patrickleboutillier/jcscpu-hmc/Videos/1- Introduction/20201125_134616.jpg

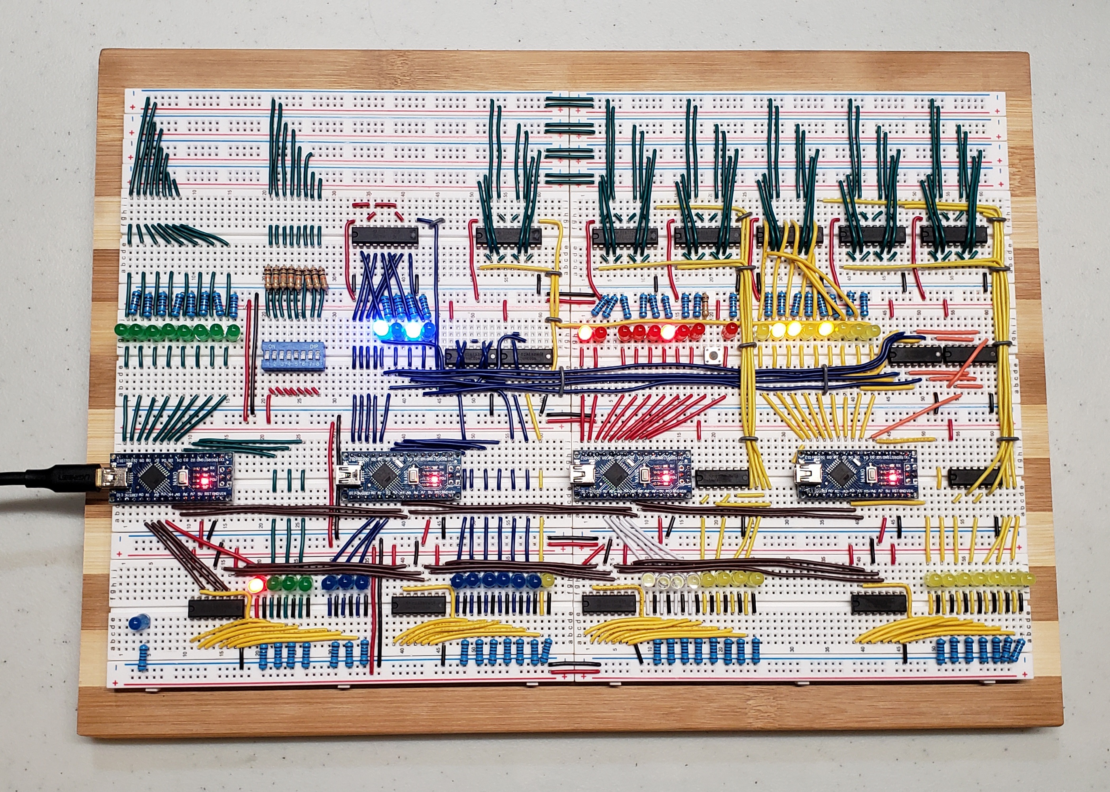
Videos/1- Introduction/20201125_134616.jpg
