patrickleboutillier/jcscpu-hmc/Videos/4- 1-bit Memory/1-bit Memory.png

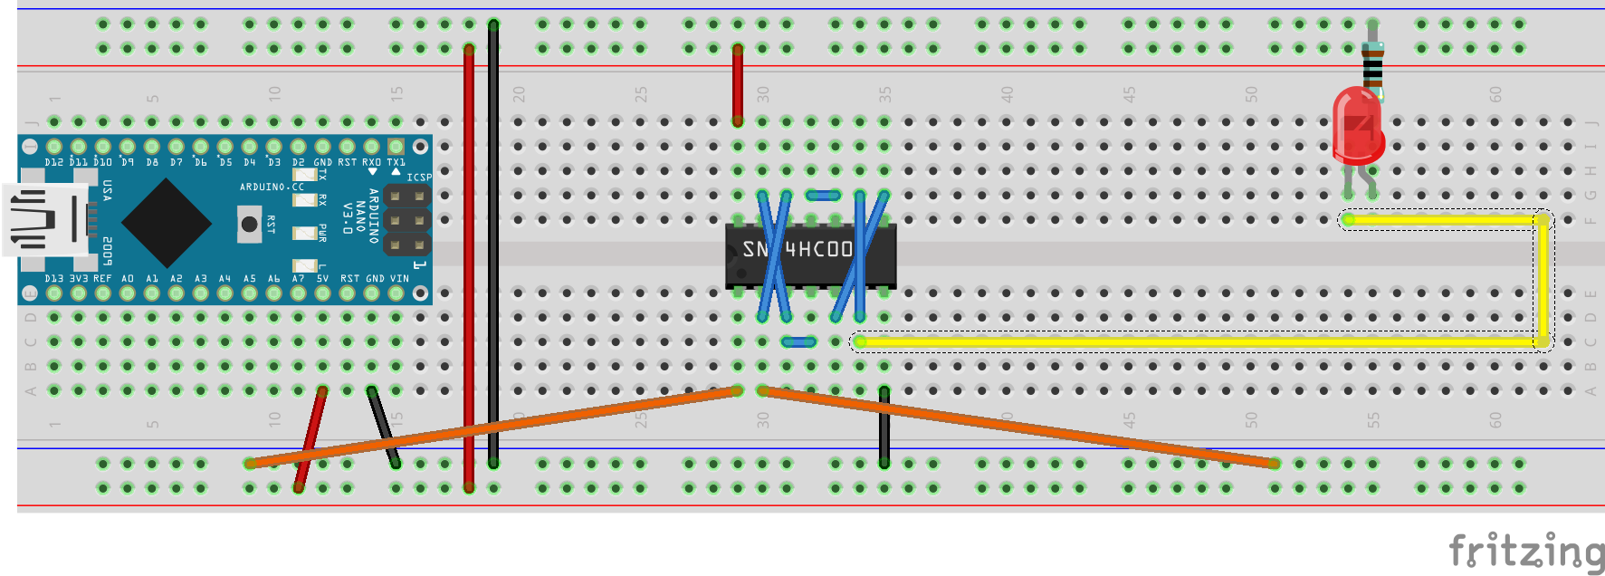
Videos/4- 1-bit Memory/1-bit Memory.png
