patrickleboutillier/jcscpu-hmc/Videos/6- The Register/Register_bb.png

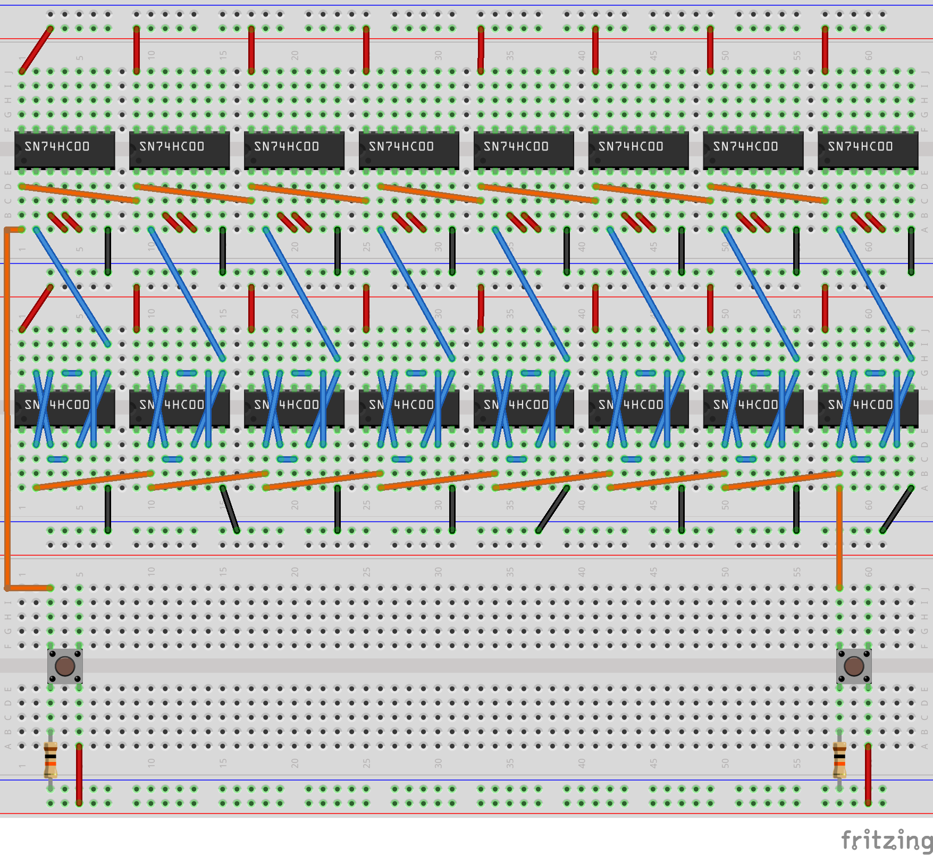
Videos/6- The Register/Register_bb.png
