patrickleboutillier/jcscpu-hmc/Videos/9- The Bus (part 2)/jcscpu-hmc_bb_bus.png

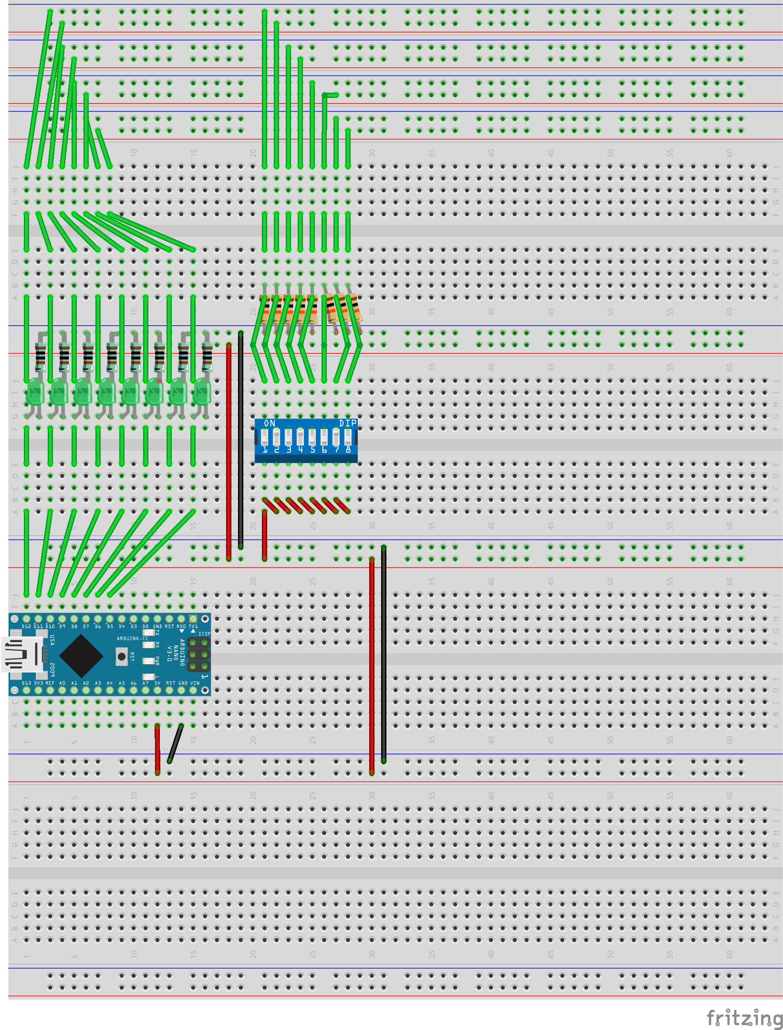
Videos/9- The Bus (part 2)/jcscpu-hmc_bb_bus.png
