patrickleboutillier/jcscpu-hmc/Videos/11- The RAM/jcscpu-hmc_bb_ram.png

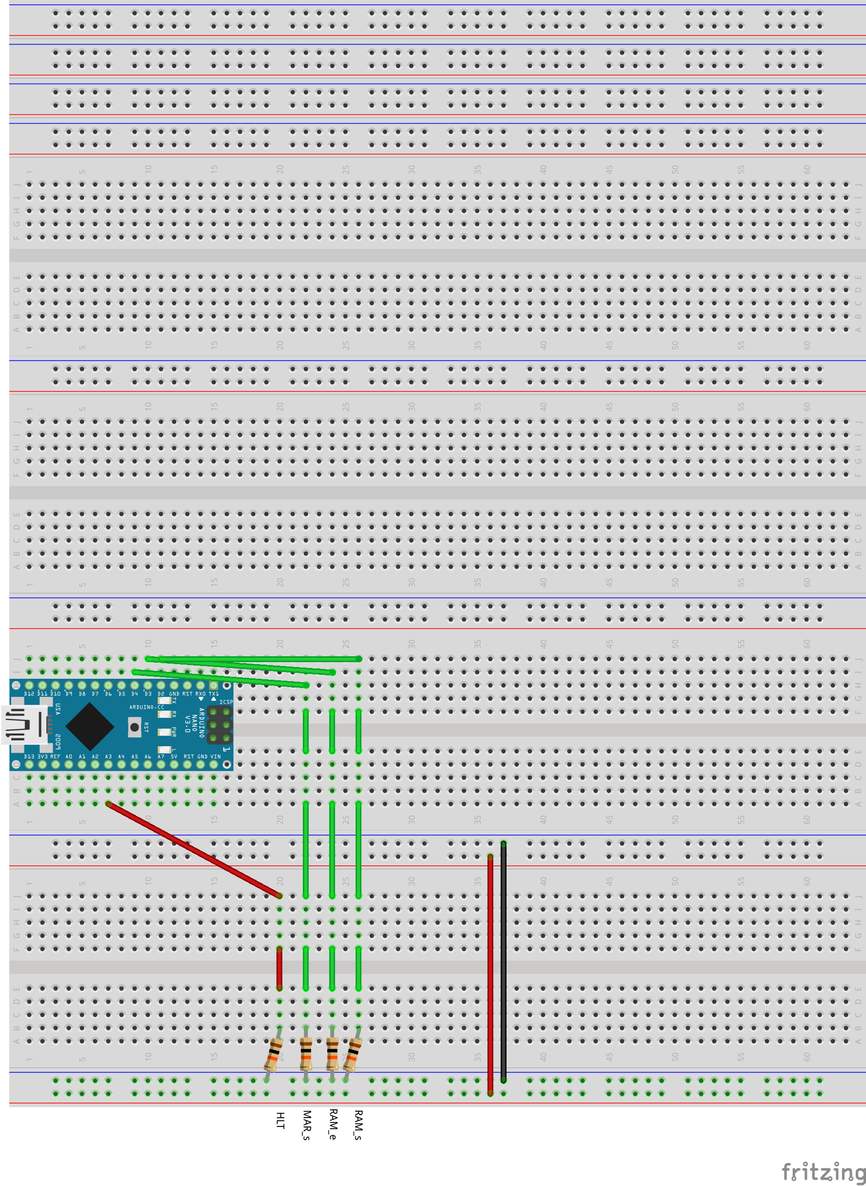
Videos/11- The RAM/jcscpu-hmc_bb_ram.png
