patrickleboutillier/jcscpu-hmc/Videos/11- The RAM/RAM.png

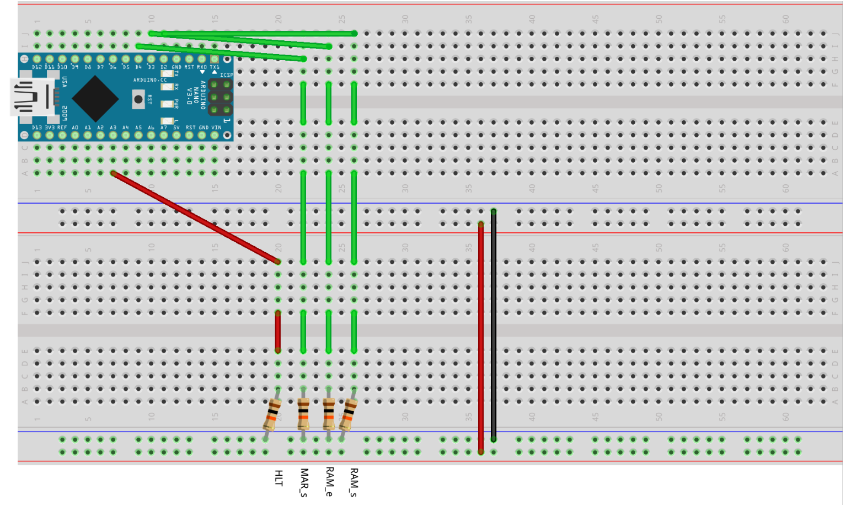
Videos/11- The RAM/RAM.png
