patrickleboutillier/jcscpu-hmc/Videos/11- The RAM/RAM_code.png

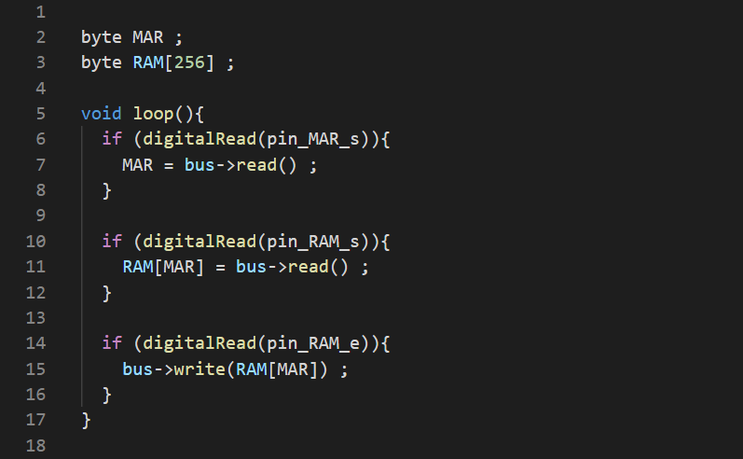
Videos/11- The RAM/RAM_code.png
