patrickleboutillier/jcscpu-hmc/Videos/13- The ALU (part1)/BOT.png

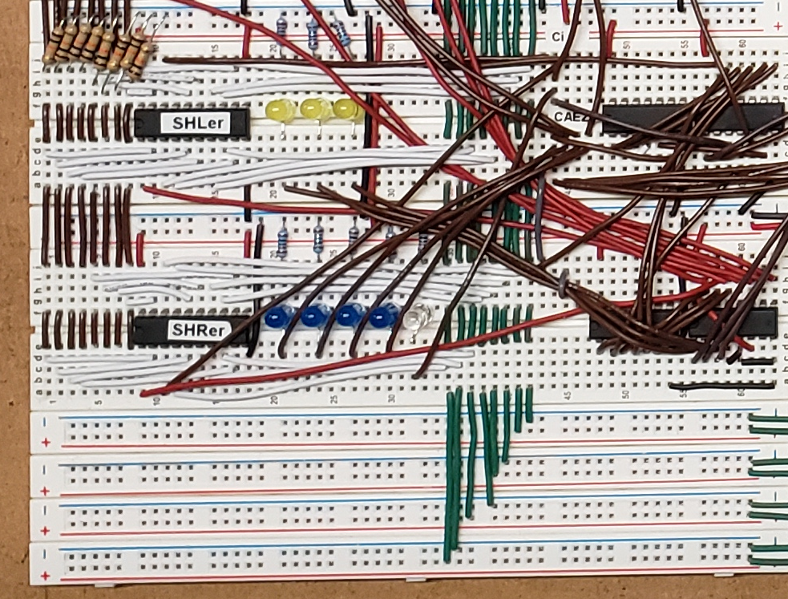
Videos/13- The ALU (part1)/BOT.png
