patrickleboutillier/jcscpu-hmc/Videos/13- The ALU (part1)/MID1.png

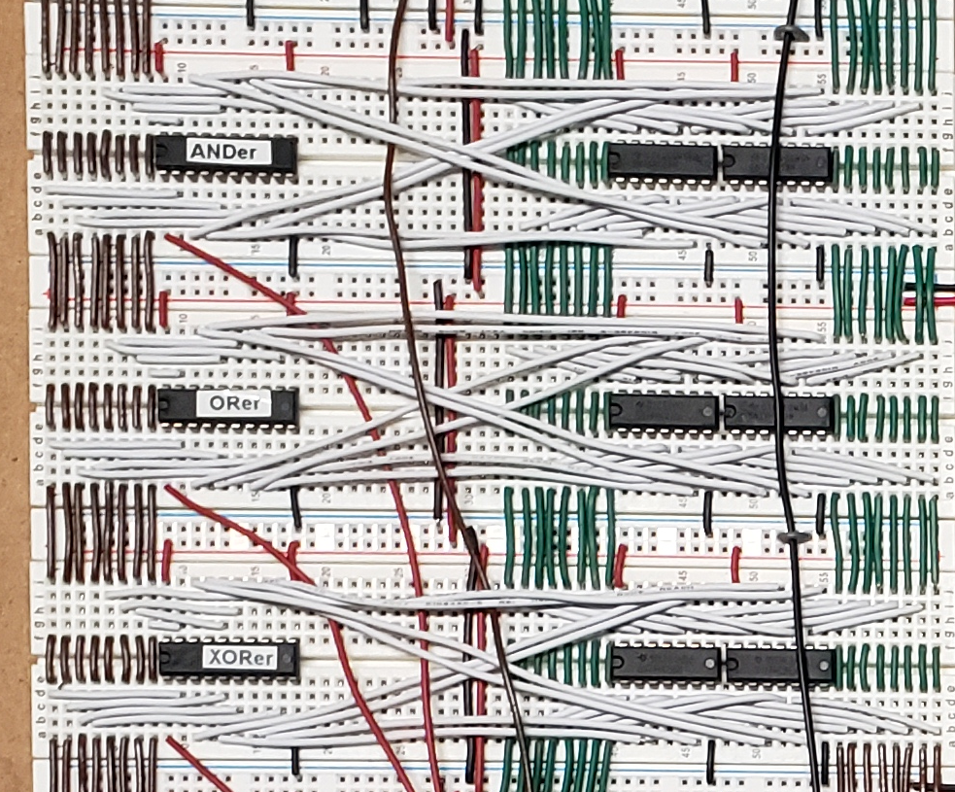
Videos/13- The ALU (part1)/MID1.png
