patrickleboutillier/jcscpu-hmc/Videos/13- The ALU (part1)/MID2.png

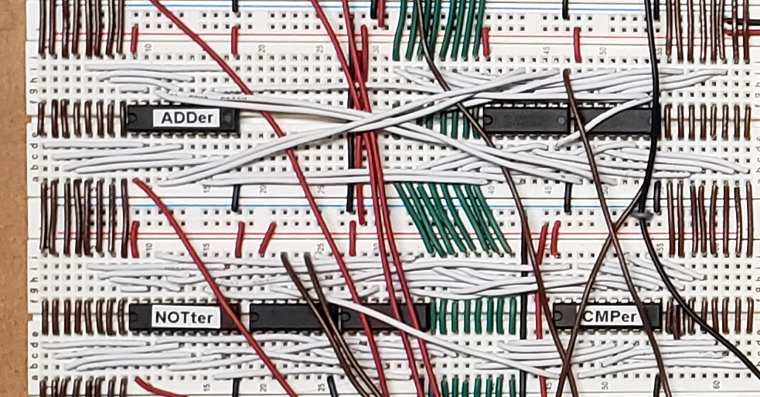
Videos/13- The ALU (part1)/MID2.png
