patrickleboutillier/jcscpu-hmc/Videos/13- The ALU (part1)/TOP.png

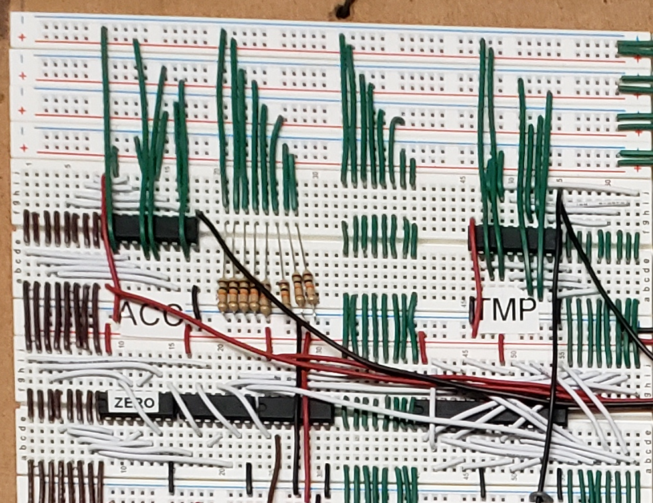
Videos/13- The ALU (part1)/TOP.png
