patrickleboutillier/jcscpu-hmc/Videos/14- The ALU (part 2)/ALU_code_1.png

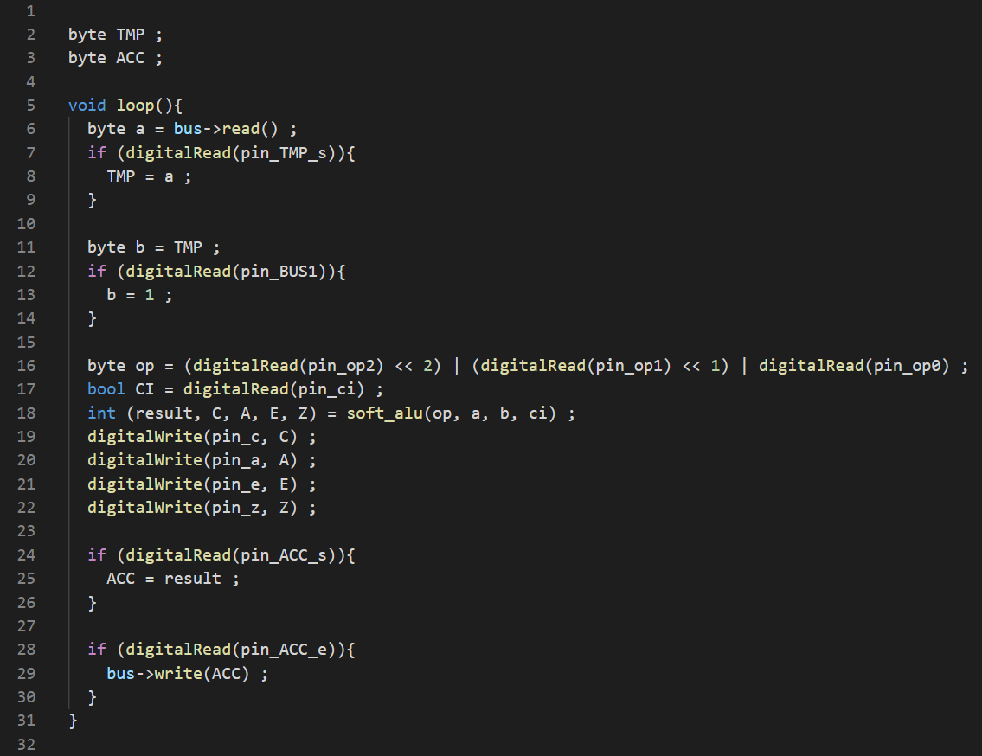
Videos/14- The ALU (part 2)/ALU_code_1.png
