patrickleboutillier/jcscpu-hmc/Videos/14- The ALU (part 2)/jcscpu-hmc_alu_bb.png

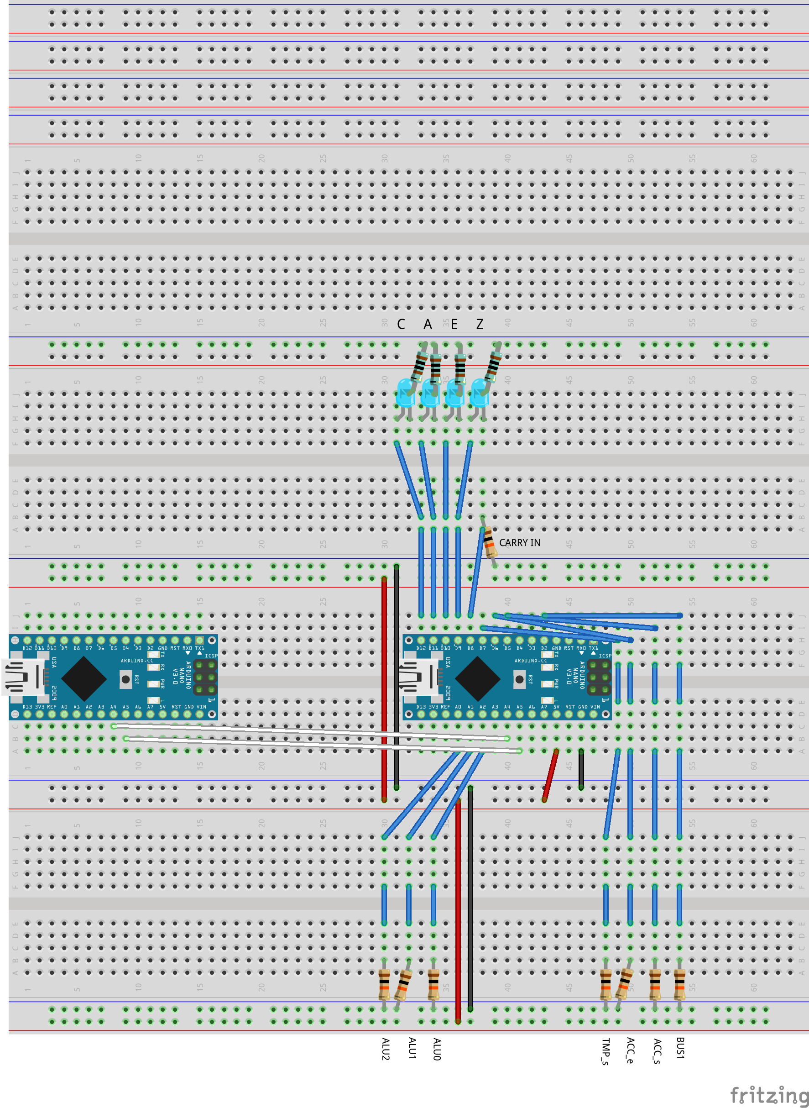
Videos/14- The ALU (part 2)/jcscpu-hmc_alu_bb.png
