patrickleboutillier/jcscpu-hmc/Videos/14- The ALU (part 2)/jcscpu-hmc_alu_bb_crop.png

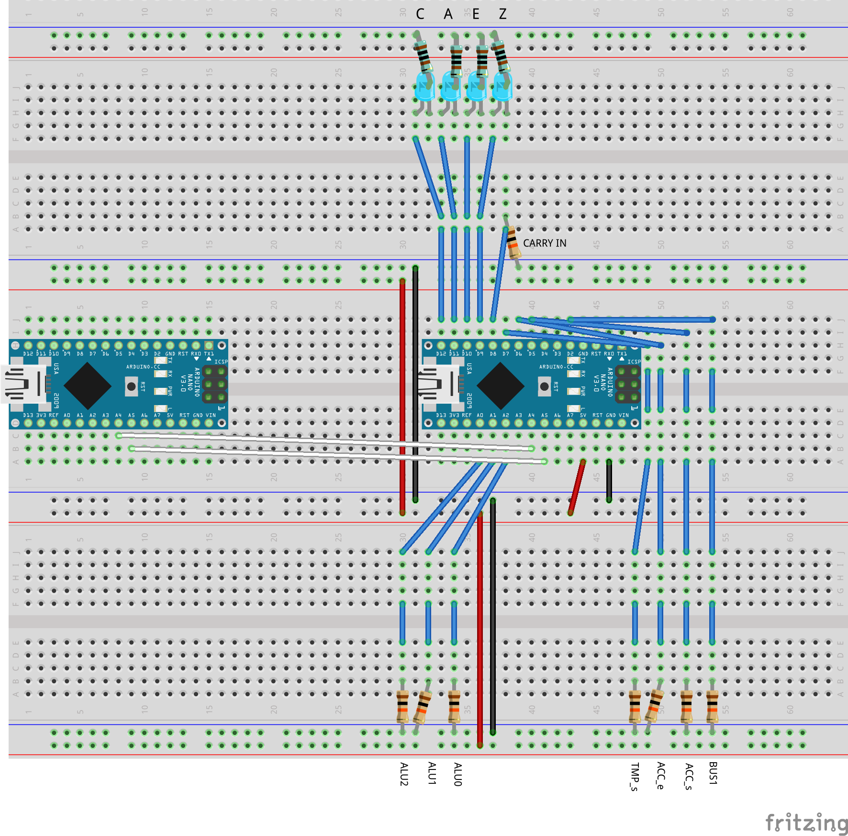
Videos/14- The ALU (part 2)/jcscpu-hmc_alu_bb_crop.png
