patrickleboutillier/jcscpu-hmc/Videos/14- The ALU (part 2)/Table.png

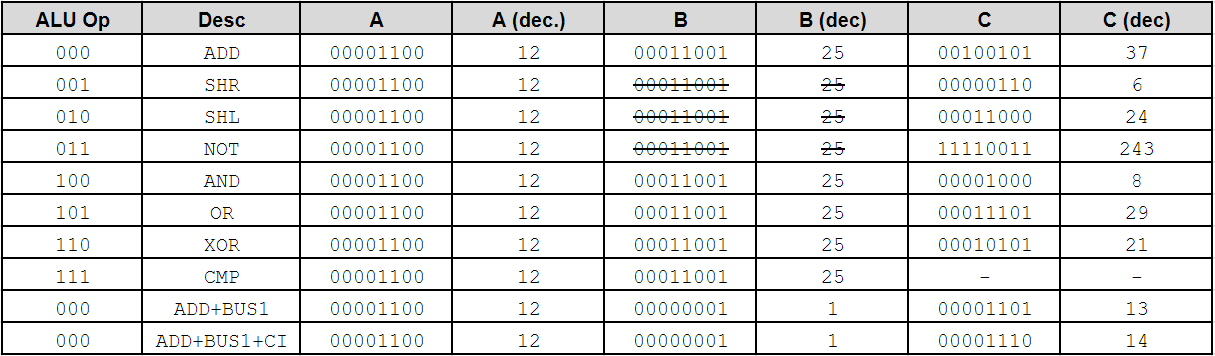
Videos/14- The ALU (part 2)/Table.png
