patrickleboutillier/jcscpu-hmc/Videos/15- The R0 and R1 Registers/jcscpu-hmc_r0r1_bb.png

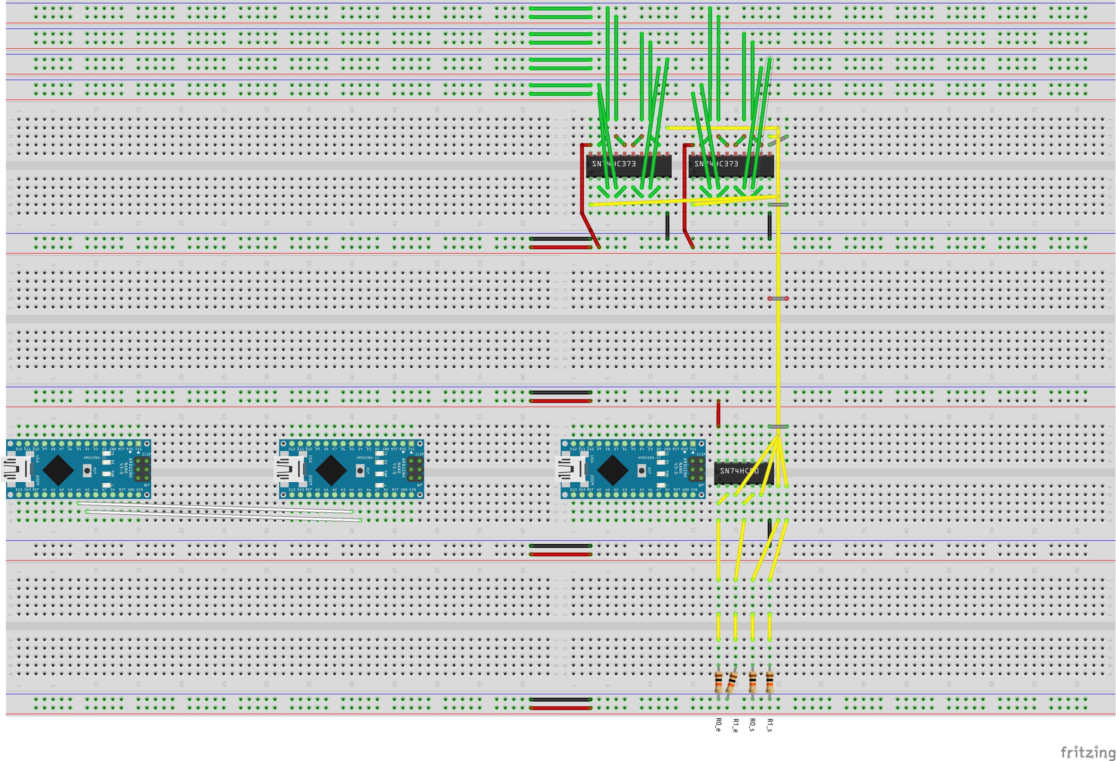
Videos/15- The R0 and R1 Registers/jcscpu-hmc_r0r1_bb.png
