patrickleboutillier/jcscpu-hmc/Videos/16- The Clock and Stepper (part 1)/Clock pulse Generator with CD4049.png

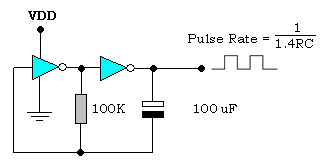
Videos/16- The Clock and Stepper (part 1)/Clock pulse Generator with CD4049.png
