patrickleboutillier/jcscpu-hmc/Videos/16- The Clock and Stepper (part 1)/Digital-Quadrature-Phase-300x210.png

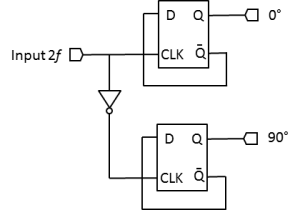
Videos/16- The Clock and Stepper (part 1)/Digital-Quadrature-Phase-300x210.png
