patrickleboutillier/jcscpu-hmc/Videos/16- The Clock and Stepper (part 1)/Flip-Flop-Outputs.png

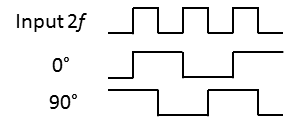
Videos/16- The Clock and Stepper (part 1)/Flip-Flop-Outputs.png
