patrickleboutillier/jcscpu-hmc/Videos/18- The Clock and Stepper (part 3)/jcscpu-hmc_clock_bb_crop.png

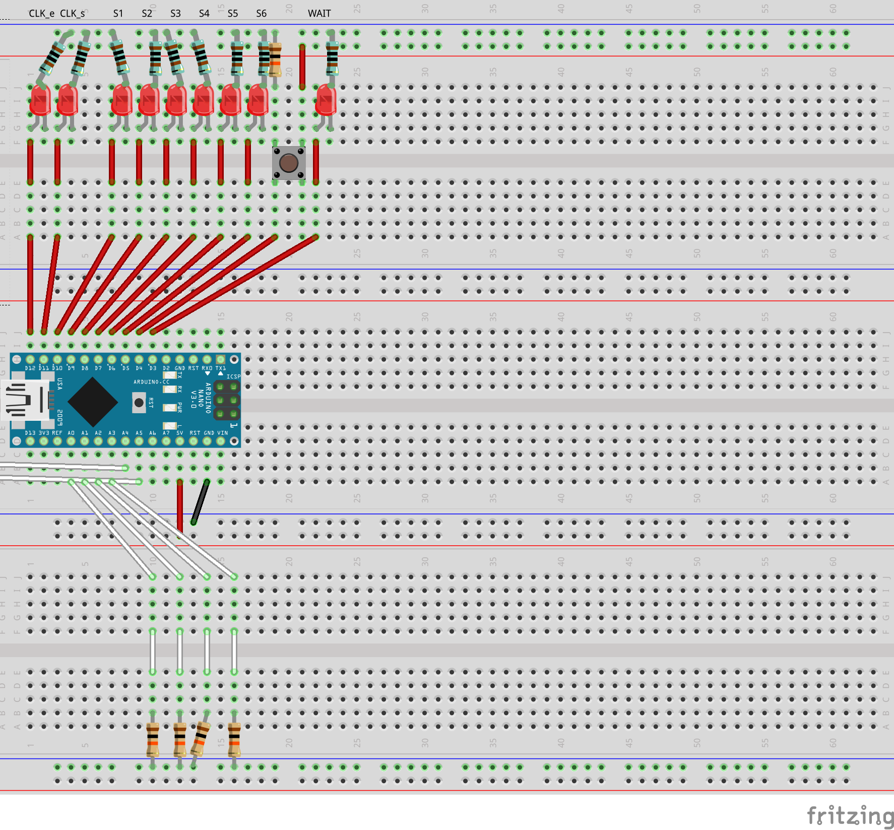
Videos/18- The Clock and Stepper (part 3)/jcscpu-hmc_clock_bb_crop.png
