patrickleboutillier/jcscpu-hmc/Videos/20- The R2 and R3 Registers/jcscpu-hmc_r2r3_bb.png

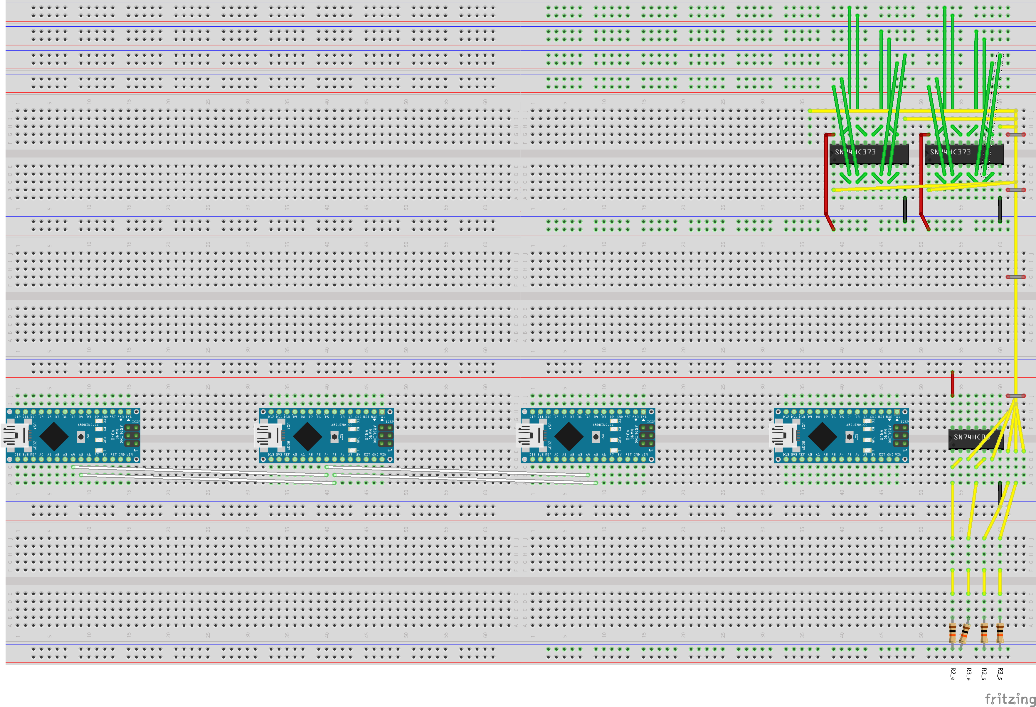
Videos/20- The R2 and R3 Registers/jcscpu-hmc_r2r3_bb.png
