patrickleboutillier/jcscpu-hmc/Videos/23- Microcode/addr0r1.png

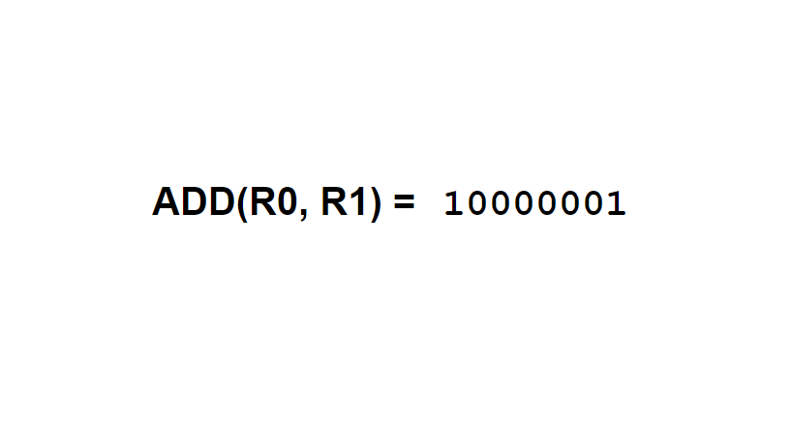
Videos/23- Microcode/addr0r1.png
