patrickleboutillier/jcscpu-hmc/Videos/23- Microcode/Arduino Nano V3.0 Twins Chip 1-550x550.jpg

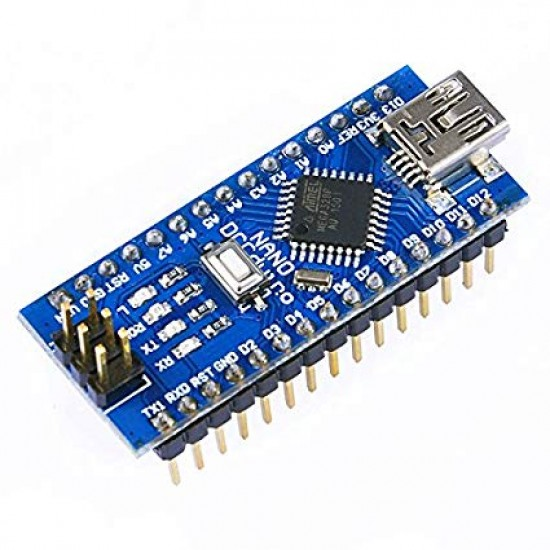
Videos/23- Microcode/Arduino Nano V3.0 Twins Chip 1-550x550.jpg
