patrickleboutillier/jcscpu-hmc/Videos/23- Microcode/CUfunc.png

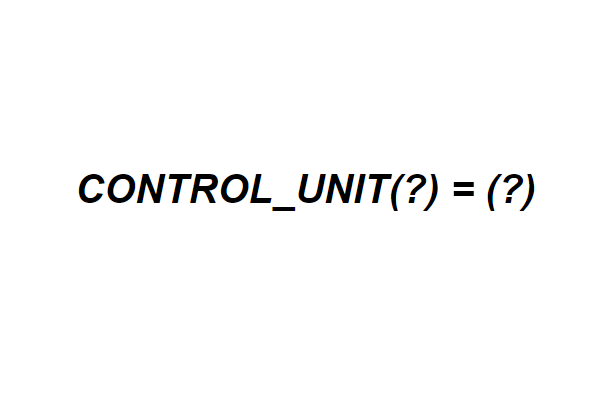
Videos/23- Microcode/CUfunc.png
