patrickleboutillier/jcscpu-hmc/Videos/23- Microcode/CUinput.png

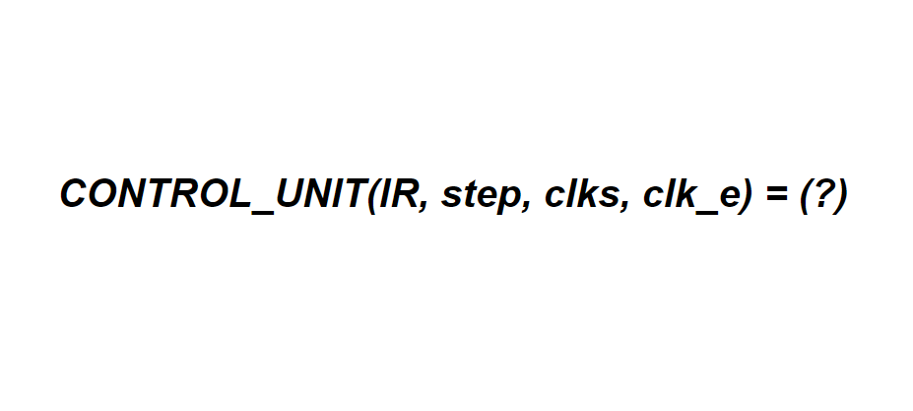
Videos/23- Microcode/CUinput.png
