patrickleboutillier/jcscpu-hmc/Videos/23- Microcode/CUinputoutput.png

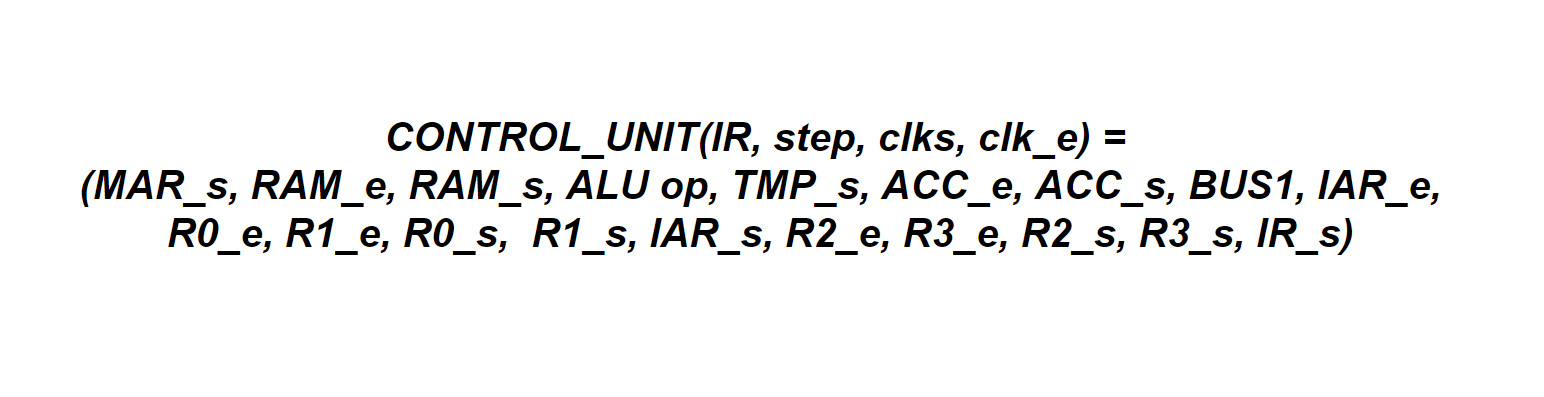
Videos/23- Microcode/CUinputoutput.png
