patrickleboutillier/jcscpu-hmc/Videos/23- Microcode/CUtable1.png

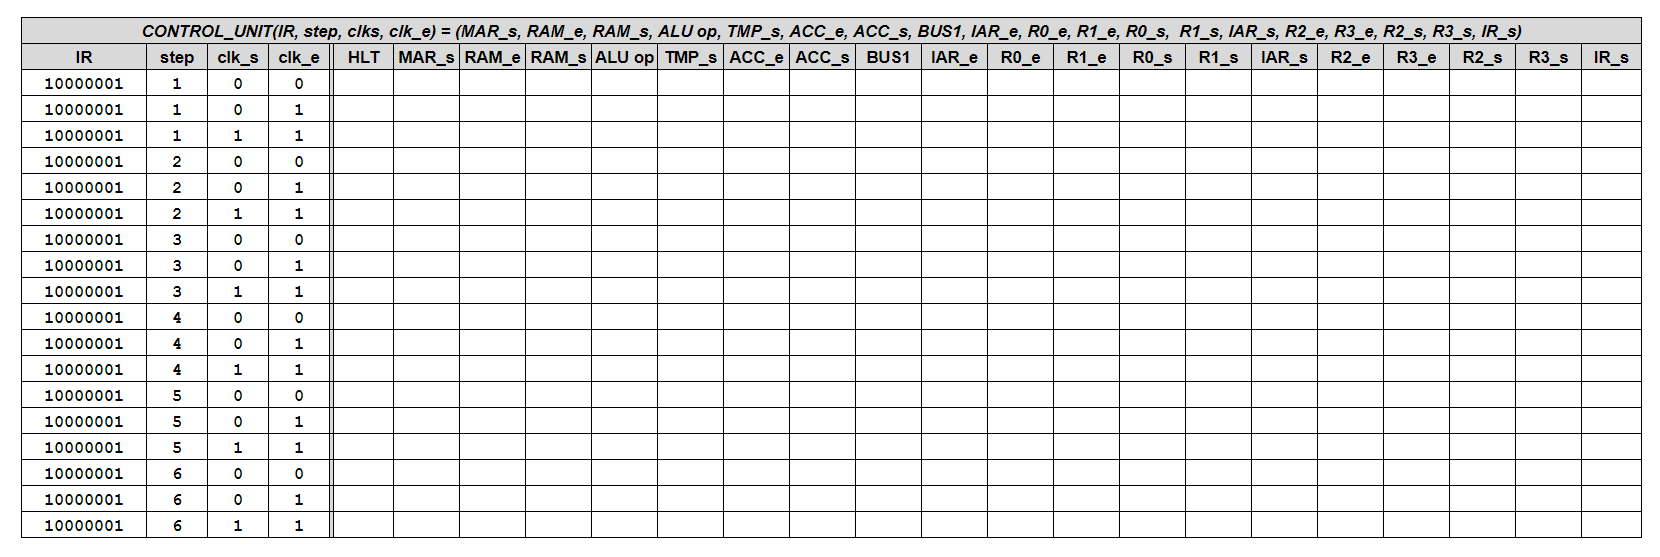
Videos/23- Microcode/CUtable1.png
