patrickleboutillier/jcscpu-hmc/Videos/23- Microcode/CUtable2.png

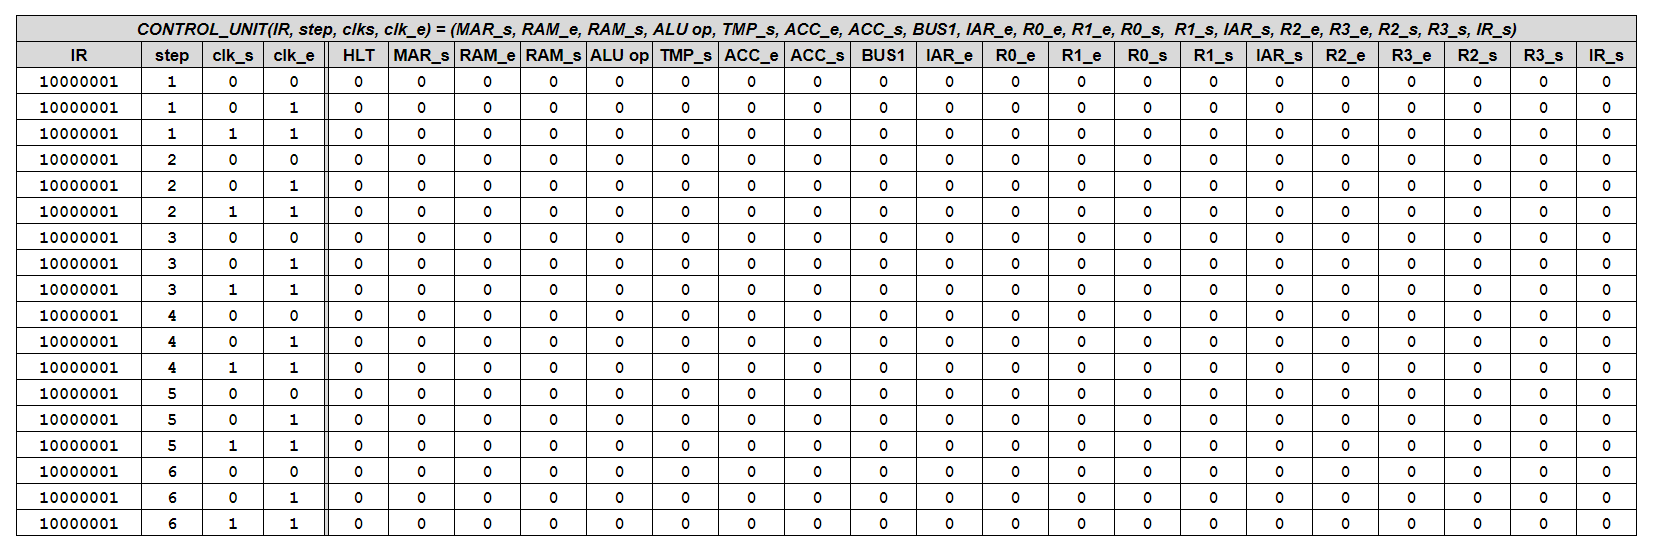
Videos/23- Microcode/CUtable2.png
