patrickleboutillier/jcscpu-hmc/Videos/23- Microcode/CUtable3.png

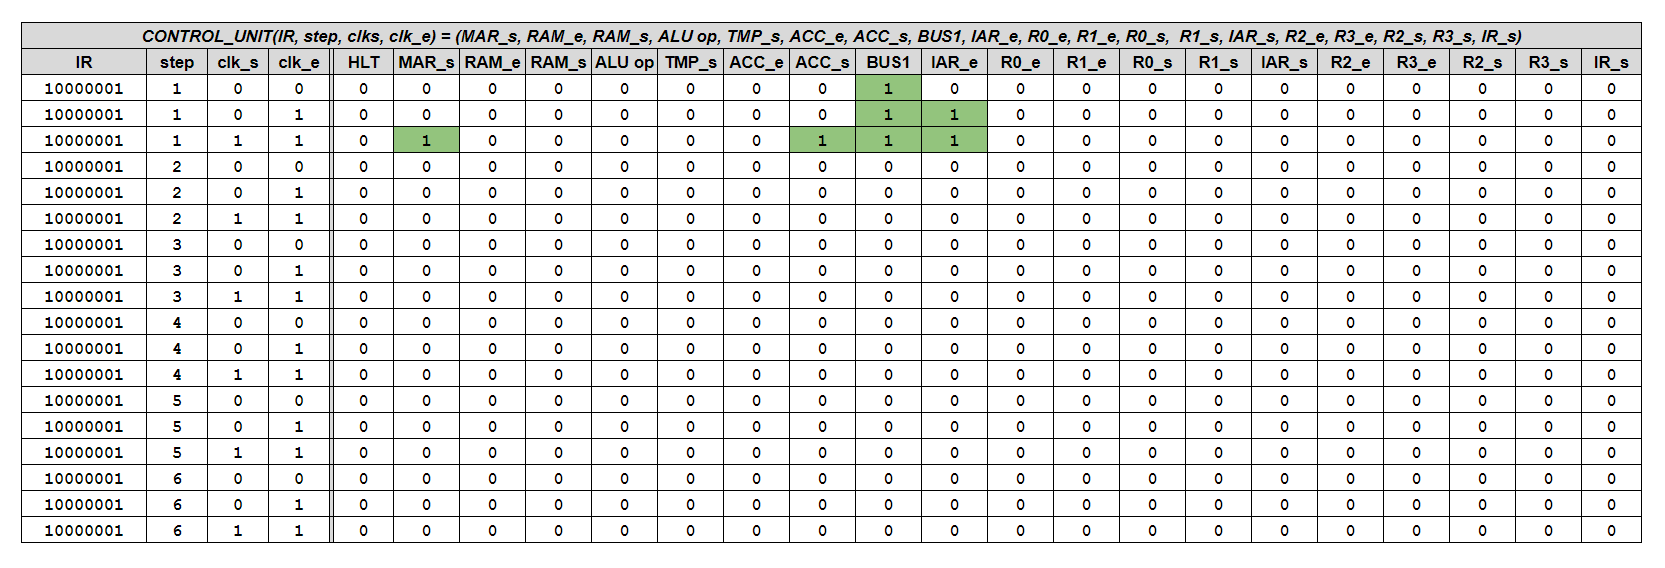
Videos/23- Microcode/CUtable3.png
