patrickleboutillier/jcscpu-hmc/Videos/23- Microcode/CUtable5.png

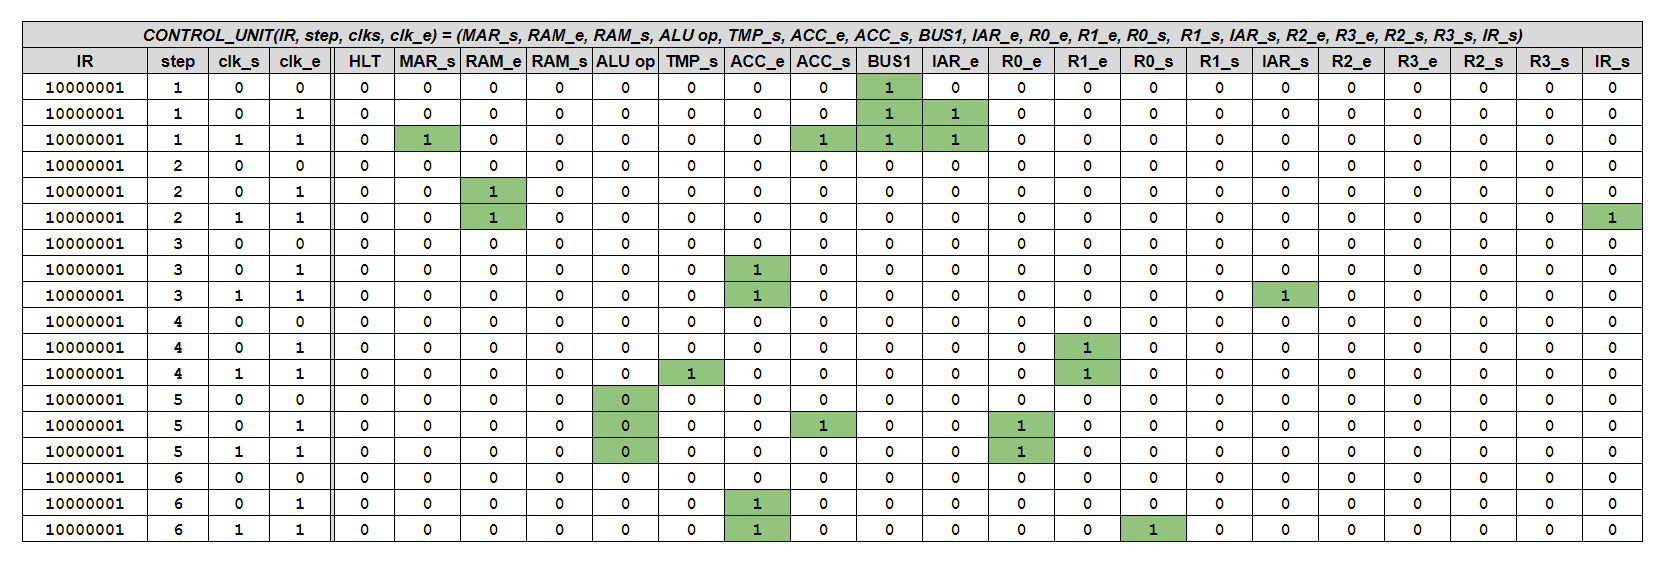
Videos/23- Microcode/CUtable5.png
