patrickleboutillier/jcscpu-hmc/Videos/23- Microcode/CUtable.png

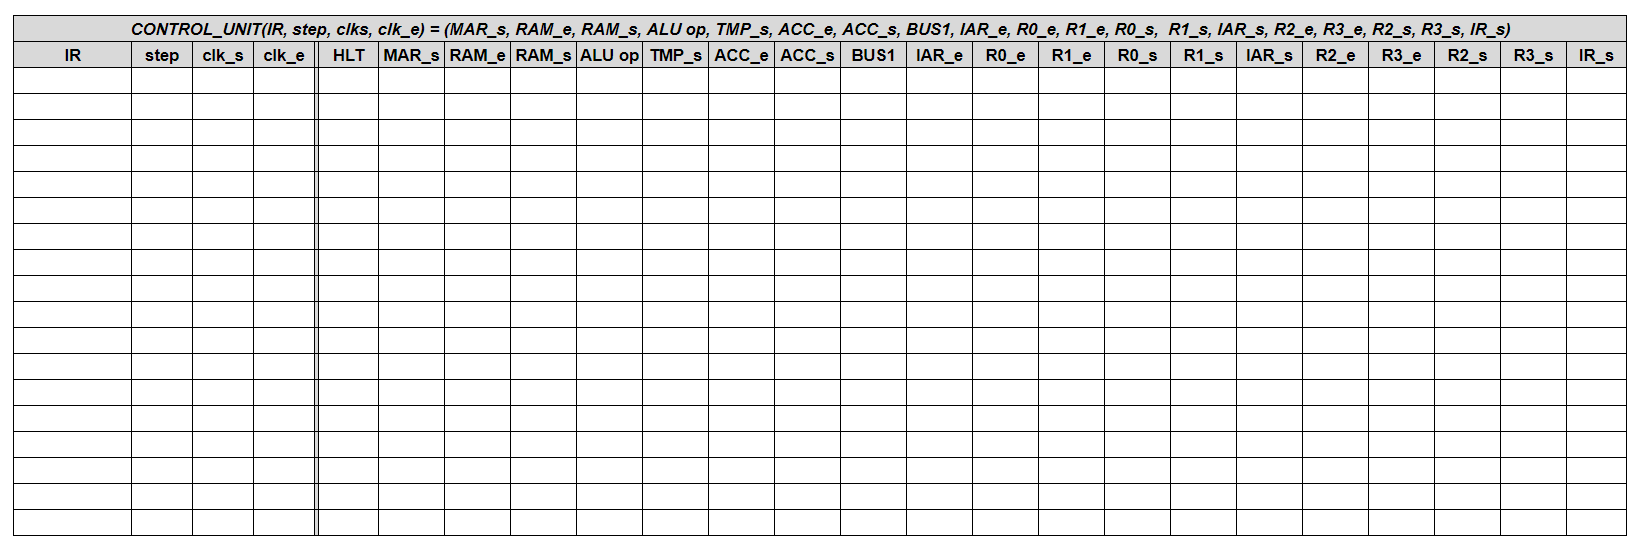
Videos/23- Microcode/CUtable.png
