patrickleboutillier/jcscpu-hmc/Videos/23- Microcode/microcode.png

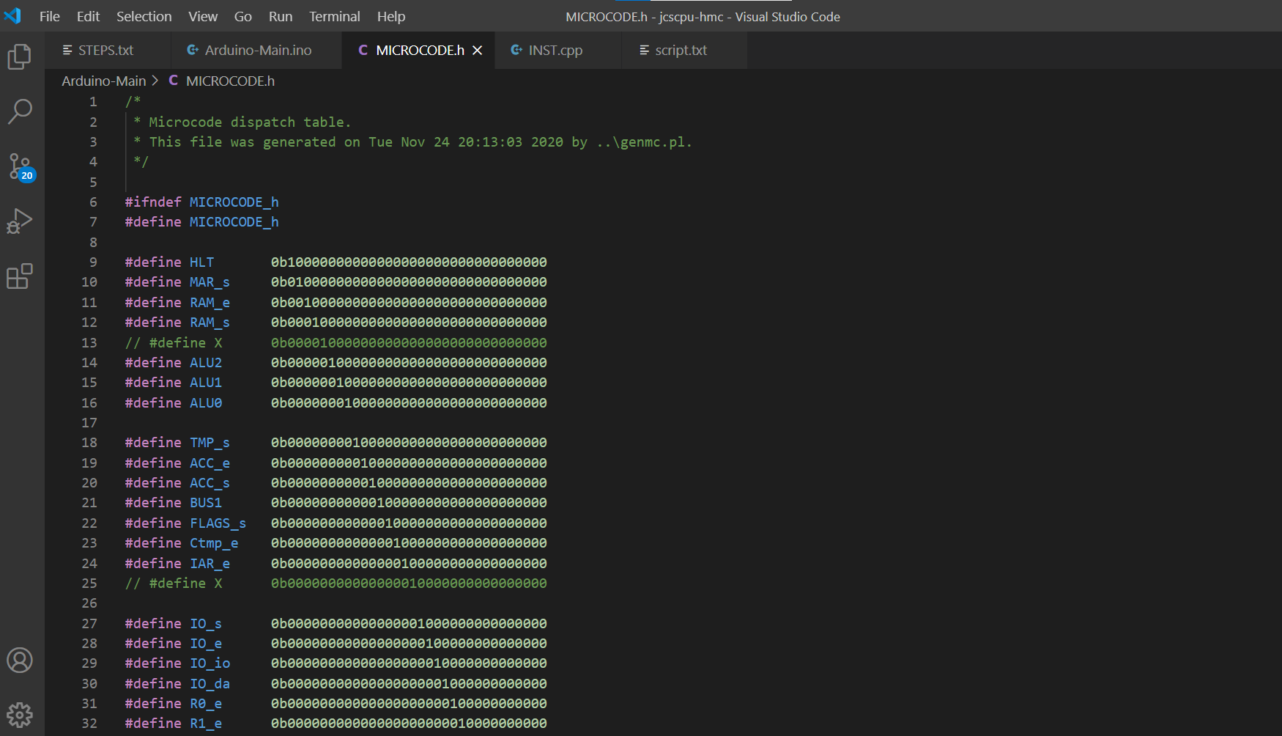
Videos/23- Microcode/microcode.png
