patrickleboutillier/jcscpu-hmc/Videos/23- Microcode/NANDtt.png

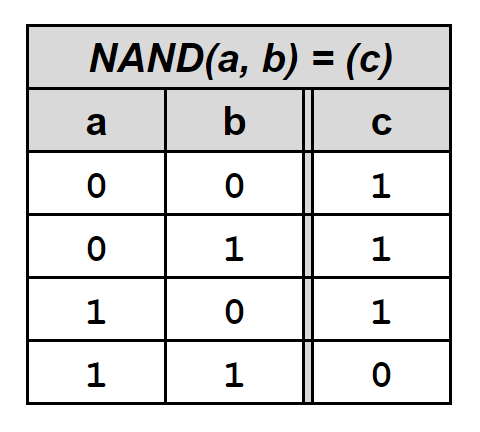
Videos/23- Microcode/NANDtt.png
