patrickleboutillier/jcscpu-hmc/Videos/23- Microcode/nanoflash.png

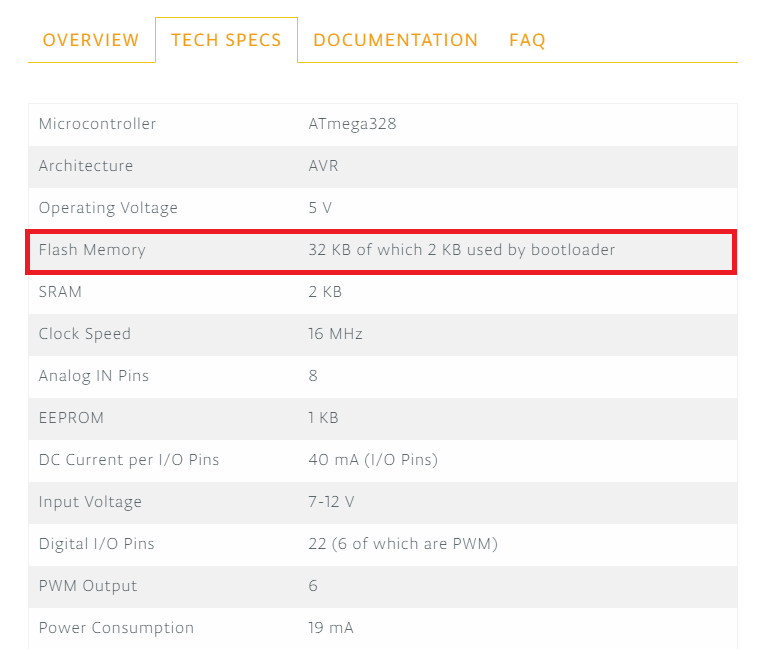
Videos/23- Microcode/nanoflash.png
