patrickleboutillier/jcscpu-hmc/Videos/23- Microcode/PIPO-SIPO.png

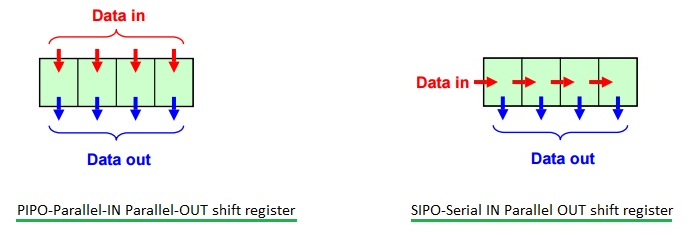
Videos/23- Microcode/PIPO-SIPO.png
