patrickleboutillier/jcscpu-hmc/Videos/23- Microcode/size1.png

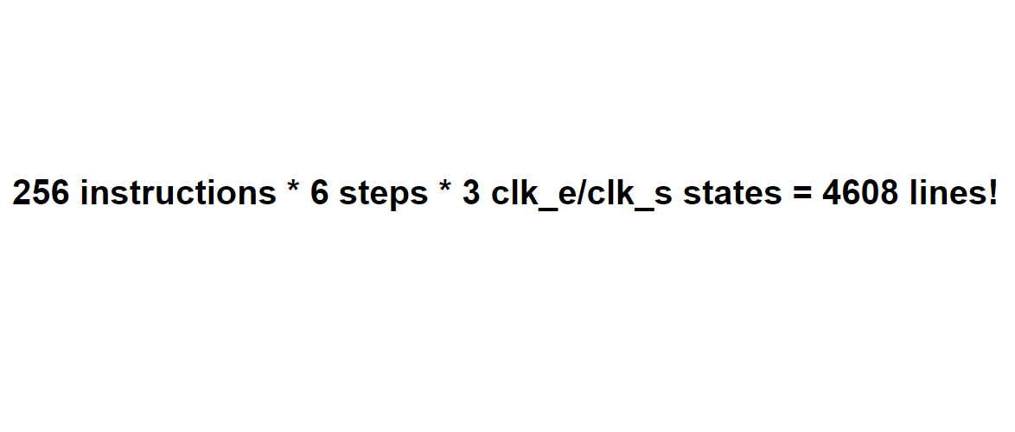
Videos/23- Microcode/size1.png
