patrickleboutillier/jcscpu-hmc/Videos/24- Shift Registers/74HC595-Shift-Register-Working.gif

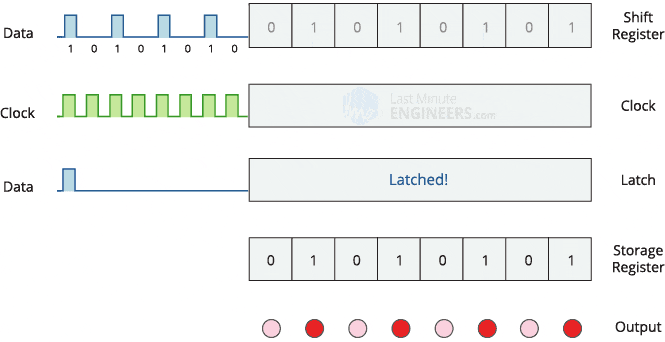
Videos/24- Shift Registers/74HC595-Shift-Register-Working.gif
