patrickleboutillier/jcscpu-hmc/Videos/24- Shift Registers/PIPO-shift-register.jpg

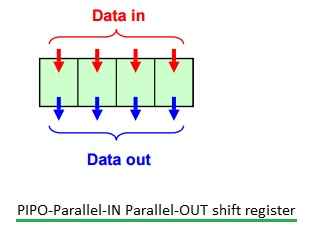
Videos/24- Shift Registers/PIPO-shift-register.jpg
