patrickleboutillier/jcscpu-hmc/Videos/24- Shift Registers/SIPO-shift-register.jpg

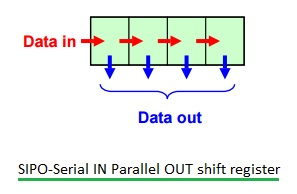
Videos/24- Shift Registers/SIPO-shift-register.jpg
