patrickleboutillier/jcscpu-hmc/Videos/25- The Control Section/code1.png

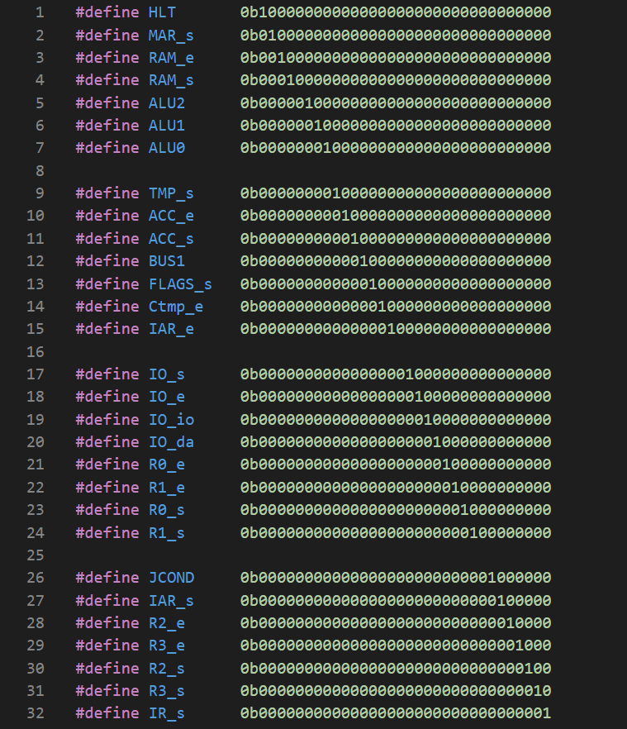
Videos/25- The Control Section/code1.png
