patrickleboutillier/jcscpu-hmc/Videos/25- The Control Section/code2.png

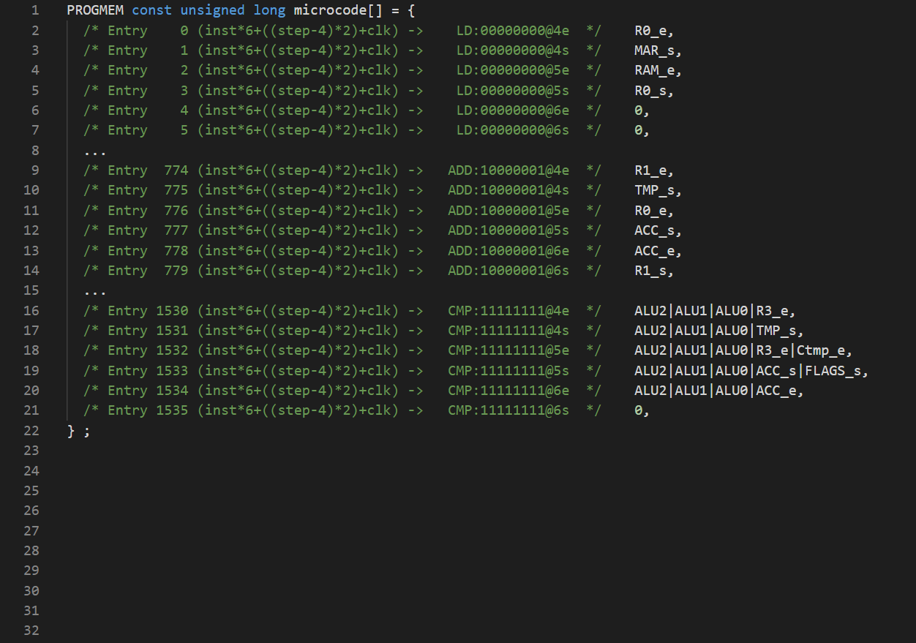
Videos/25- The Control Section/code2.png
