patrickleboutillier/jcscpu-hmc/Videos/25- The Control Section/code3.png

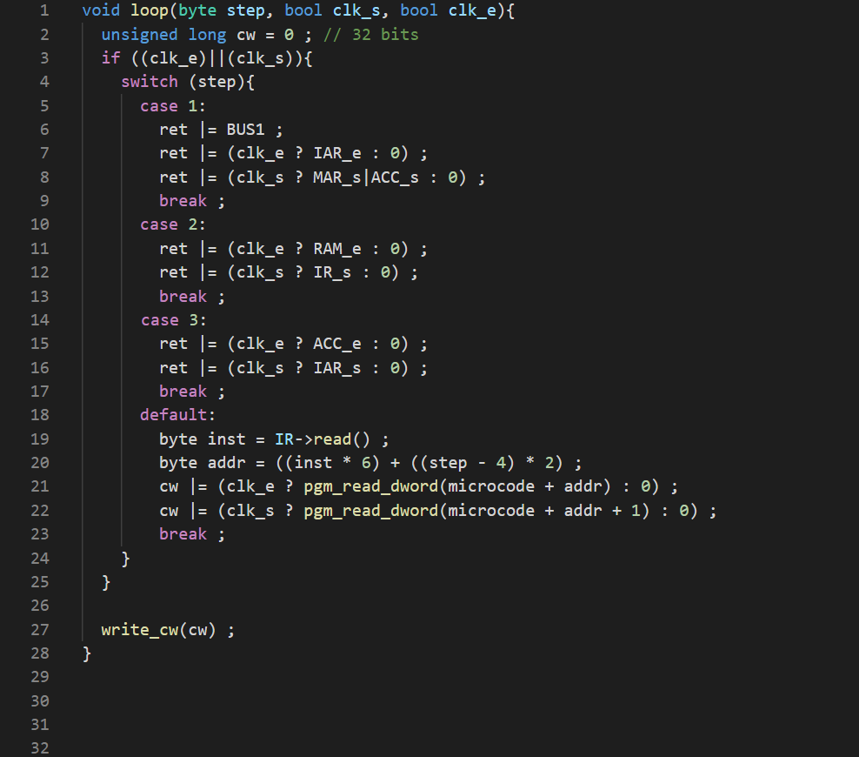
Videos/25- The Control Section/code3.png
