patrickleboutillier/jcscpu-hmc/Videos/25- The Control Section/code4.png

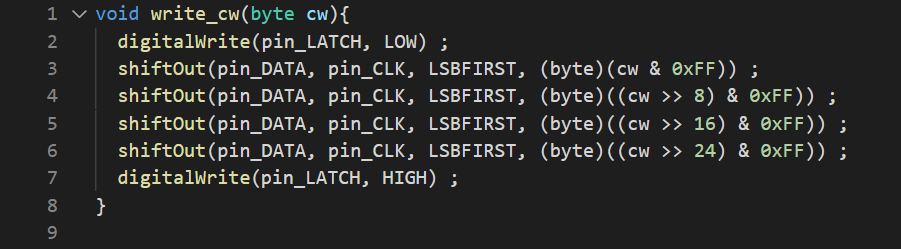
Videos/25- The Control Section/code4.png
