patrickleboutillier/jcscpu-hmc/Videos/25- The Control Section/jcscpu-hmc_cs_bb.png

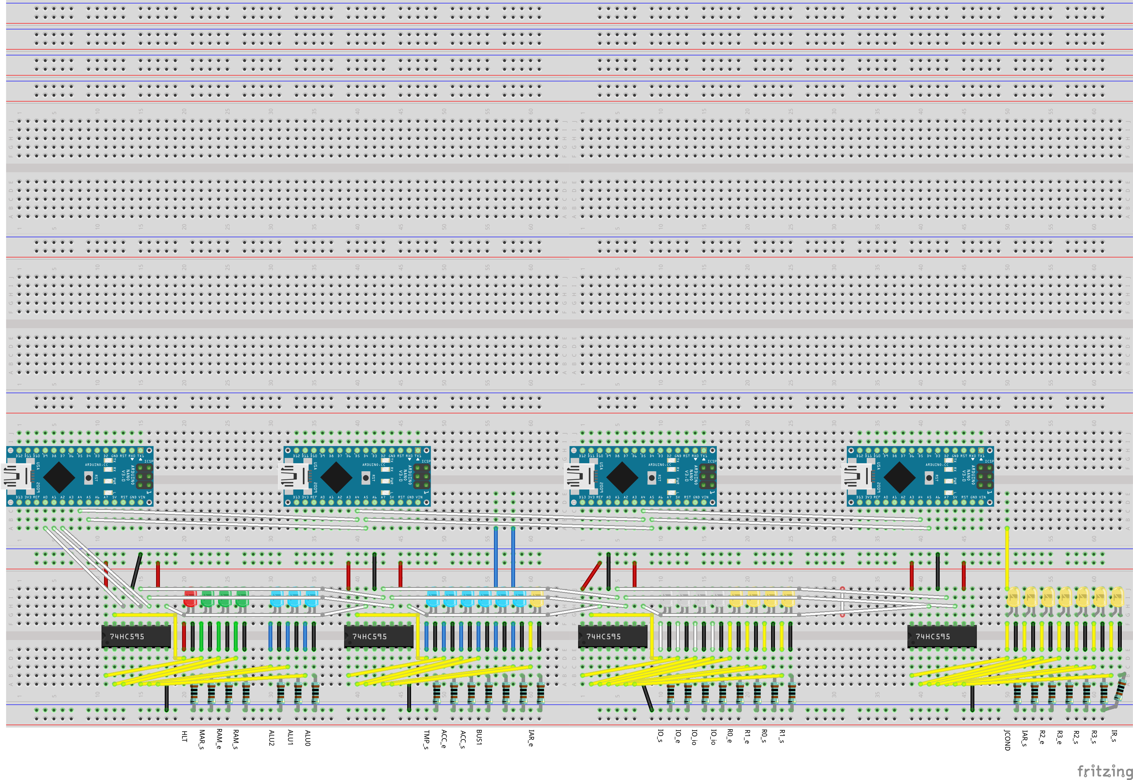
Videos/25- The Control Section/jcscpu-hmc_cs_bb.png
