patrickleboutillier/jcscpu-hmc/Videos/28- The FLAGS Register and JCAEZ Circuitry/jcscpu-hmc_flag_lines_bb.png

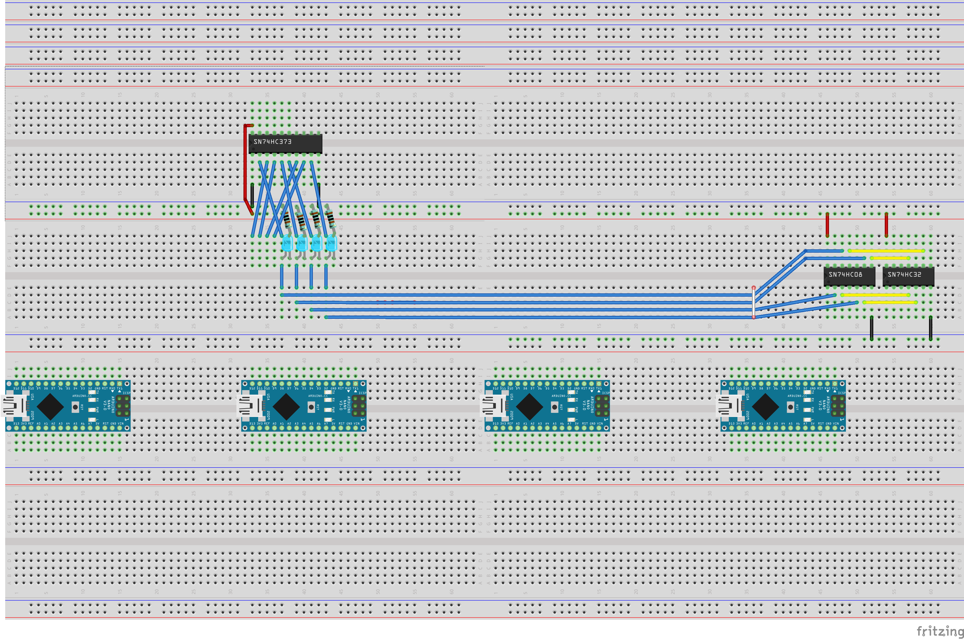
Videos/28- The FLAGS Register and JCAEZ Circuitry/jcscpu-hmc_flag_lines_bb.png
