patrickleboutillier/jcscpu-hmc/Videos/28- The FLAGS Register and JCAEZ Circuitry/jcscpu-hmc_flags_bb.png

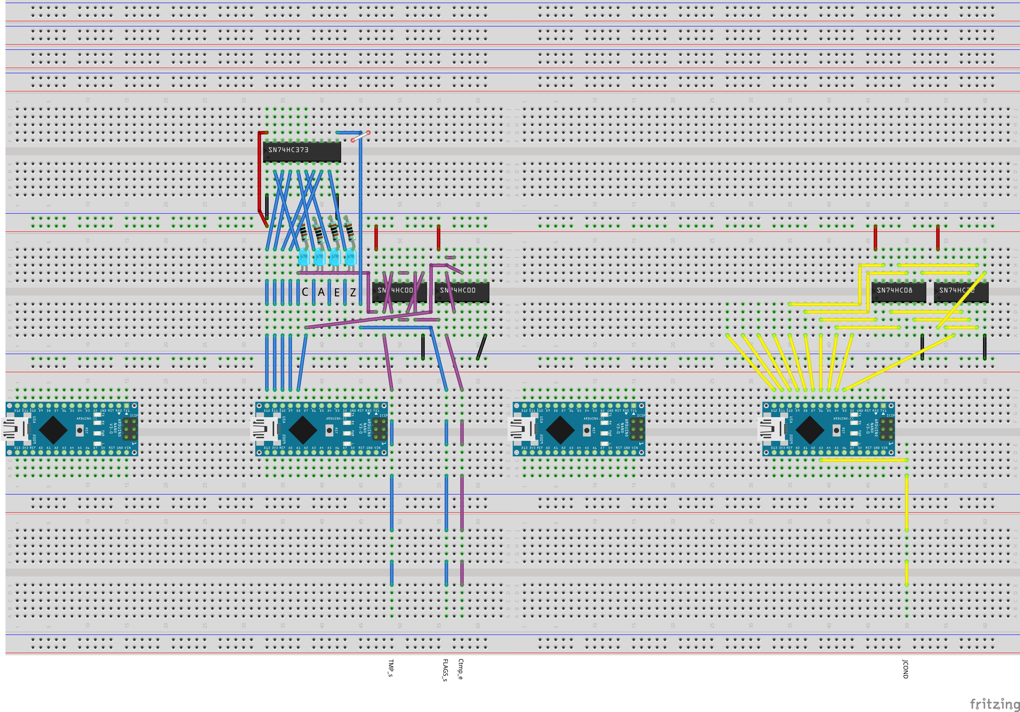
Videos/28- The FLAGS Register and JCAEZ Circuitry/jcscpu-hmc_flags_bb.png
