patrickleboutillier/jcscpu-hmc/Videos/31- Running Sample Programs/c64.png

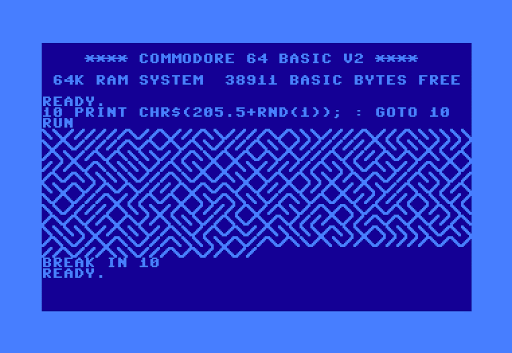
Videos/31- Running Sample Programs/c64.png
