patrickleboutillier/jcscpu-hmc/Videos/31- Running Sample Programs/EDSAC_(12).jpg

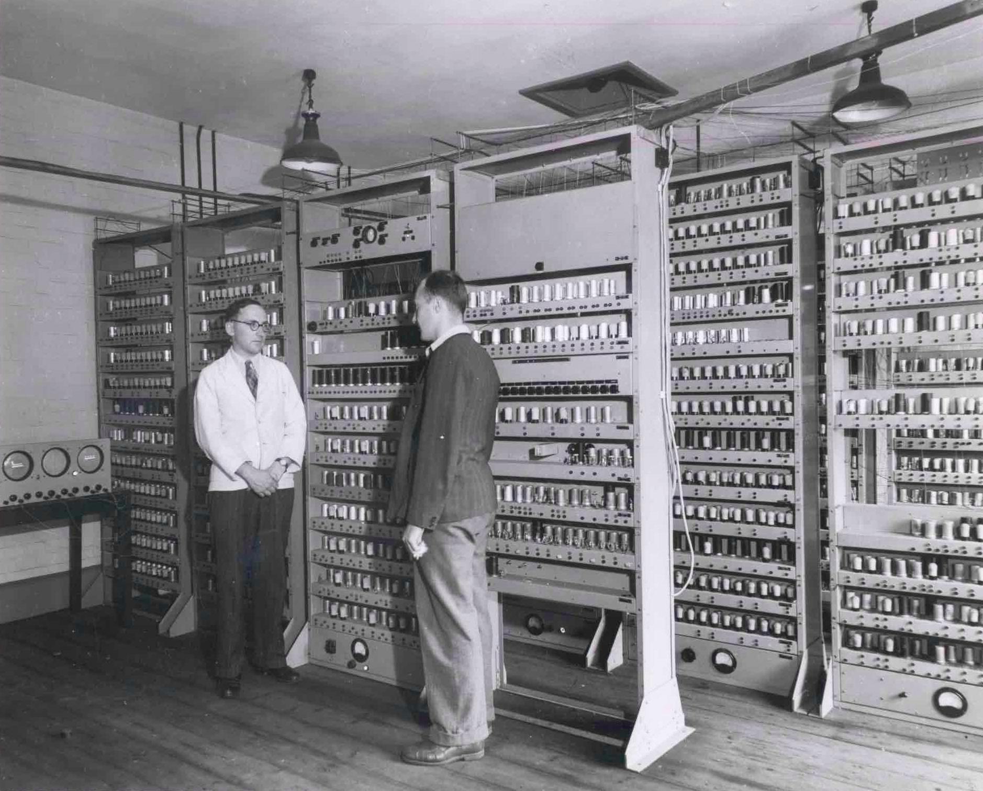
Videos/31- Running Sample Programs/EDSAC_(12).jpg
