patrickleboutillier/jcscpu-hmc/Videos/31- Running Sample Programs/prog5x5.png

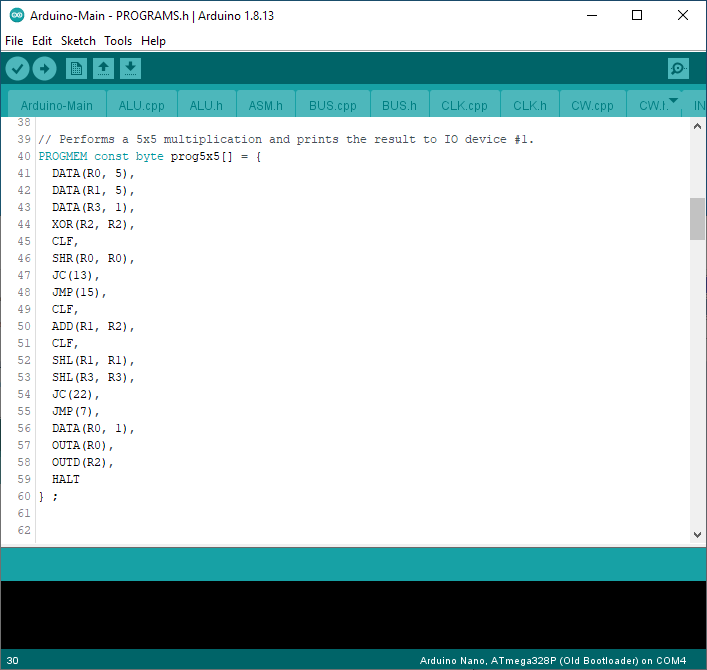
Videos/31- Running Sample Programs/prog5x5.png
