patrickleboutillier/jcscpu-hmc/Videos/31- Running Sample Programs/progggame.png

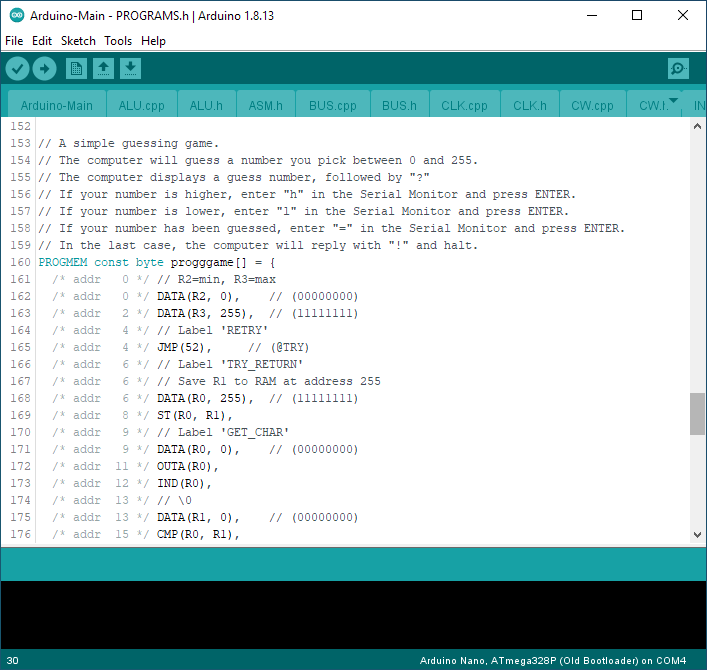
Videos/31- Running Sample Programs/progggame.png
