patrickleboutillier/jcscpu-hmc/Videos/31- Running Sample Programs/progjc.png

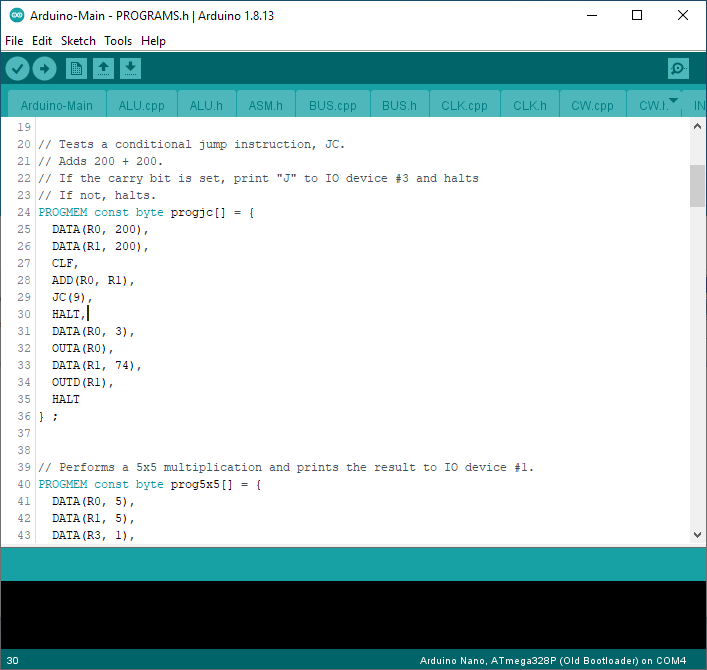
Videos/31- Running Sample Programs/progjc.png
