patrickleboutillier/jcscpu-hmc/Videos/31- Running Sample Programs/progsquares.png

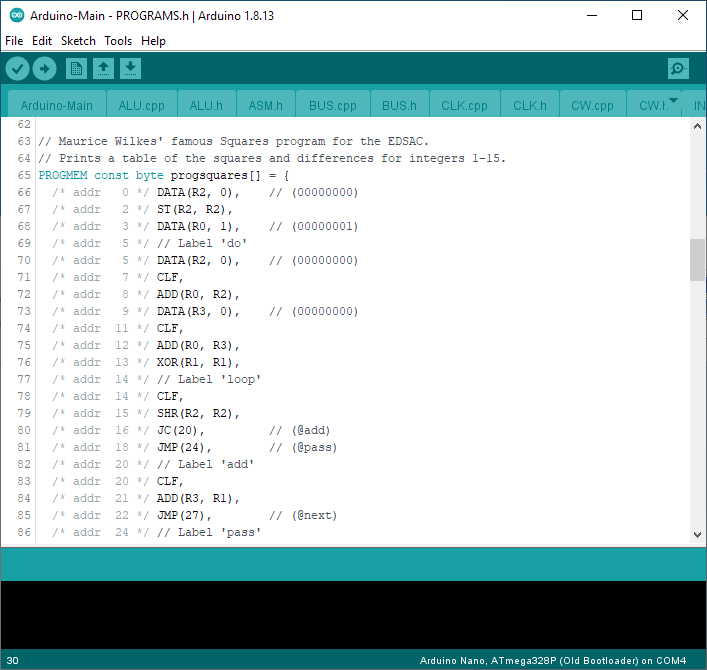
Videos/31- Running Sample Programs/progsquares.png
