patrickleboutillier/jcscpu-hmc/Videos/32- Conclusion/555.png

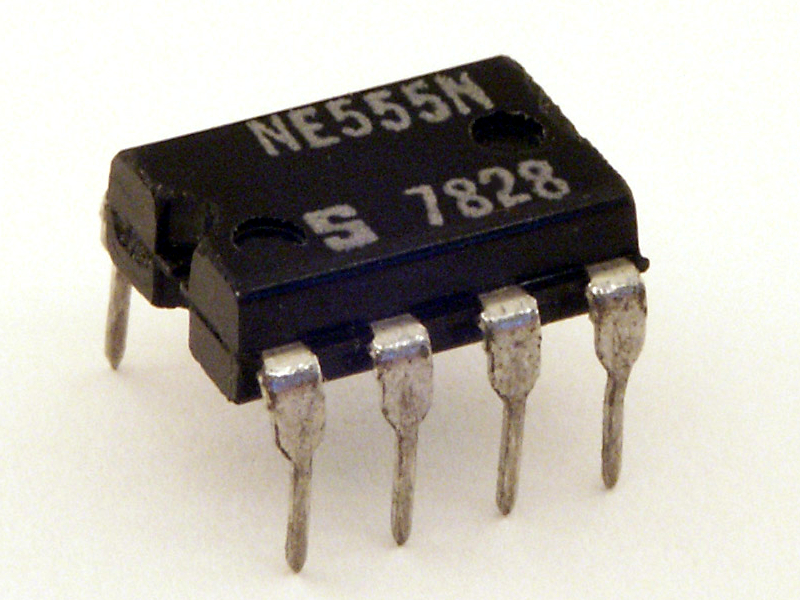
Videos/32- Conclusion/555.png
