patrickleboutillier/jcscpu-hmc/Videos/21- Instruction Processing/Instructions.png

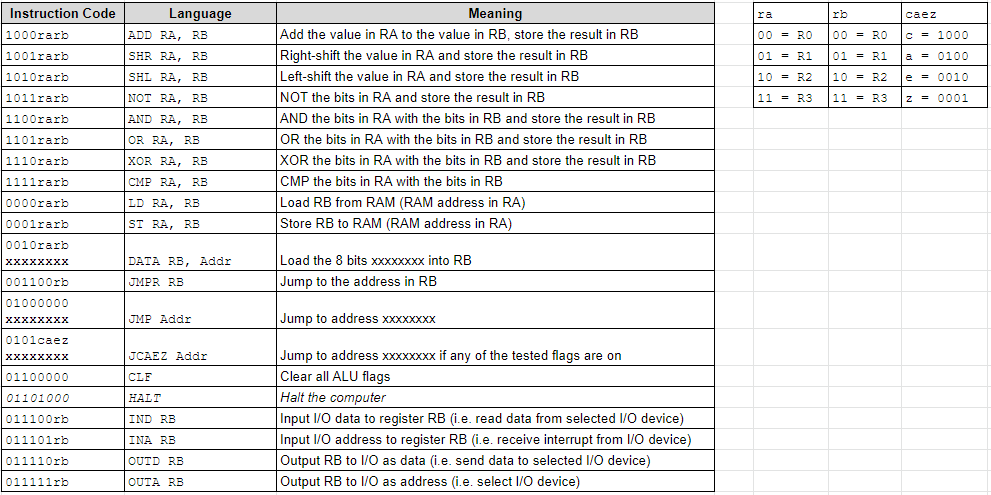
Videos/21- Instruction Processing/Instructions.png
