patrickleboutillier/jcscpu-hmc/Videos/21- Instruction Processing/jcscpu-hmc_ir_iar_bb.png

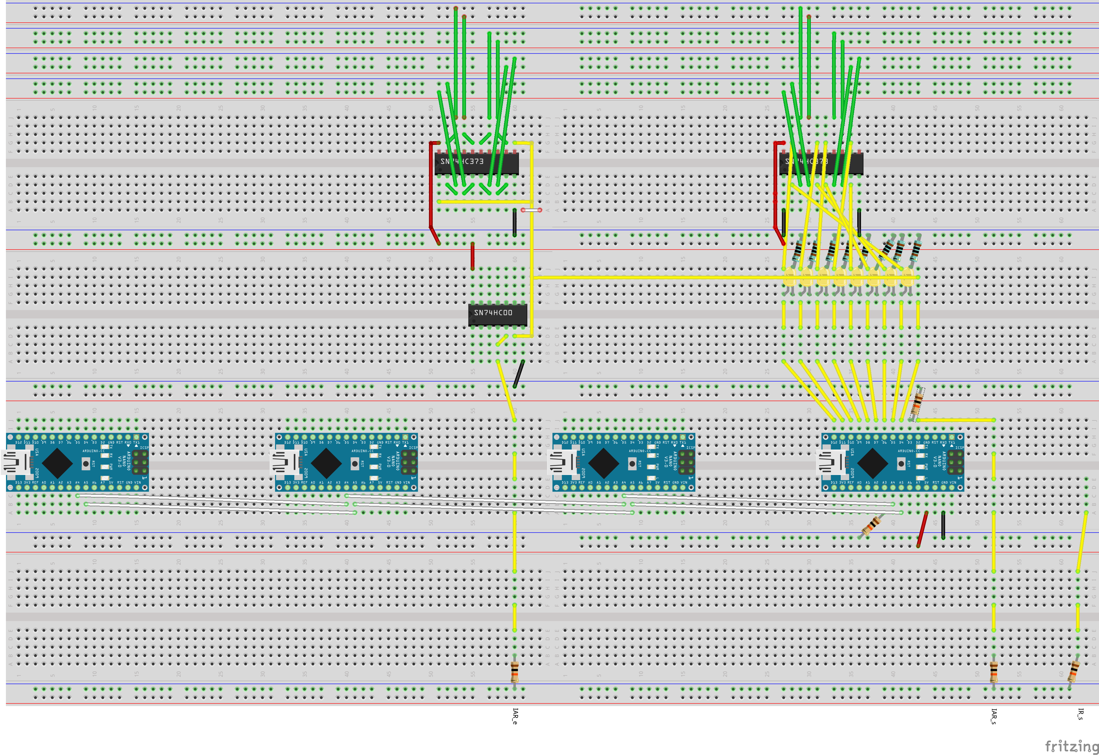
Videos/21- Instruction Processing/jcscpu-hmc_ir_iar_bb.png
