patrickleboutillier/jcscpu-hmc/Videos/26- Manual Programming/prog.png

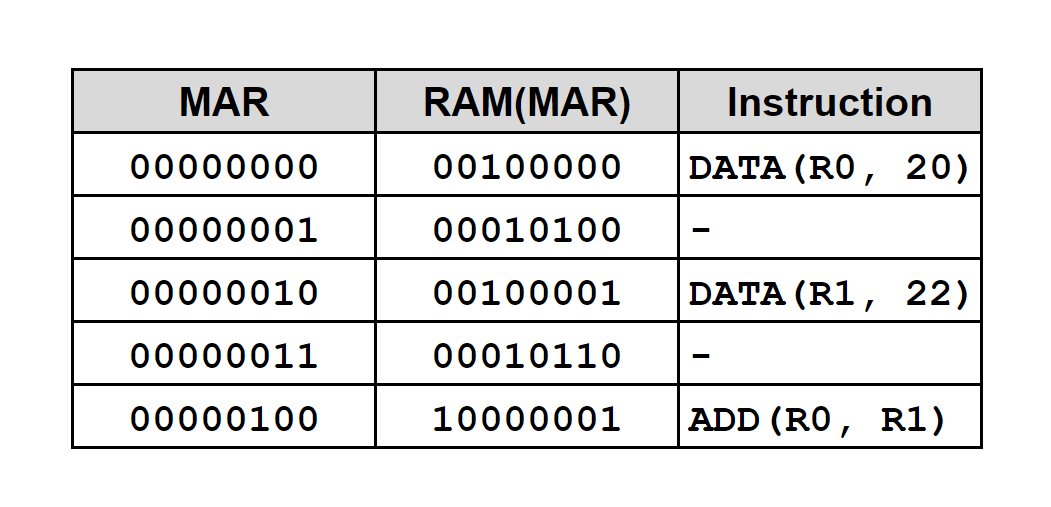
Videos/26- Manual Programming/prog.png
