patrickleboutillier/jcscpu-hmc/Videos/29- The IO Instructions and Devices/IOinsts.png

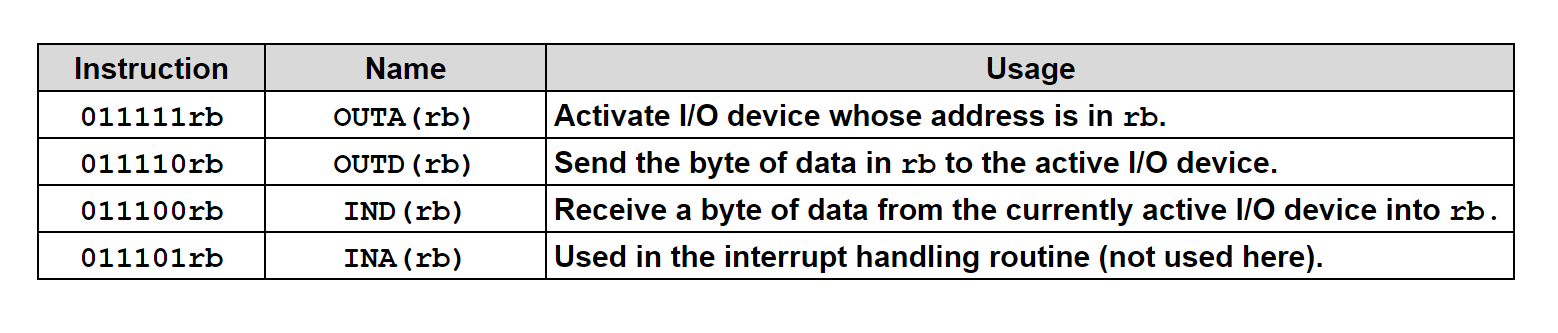
Videos/29- The IO Instructions and Devices/IOinsts.png
