patrickleboutillier/jcscpu-hmc/Videos/30- Assembly Language and Automatic Clock/asm1.png

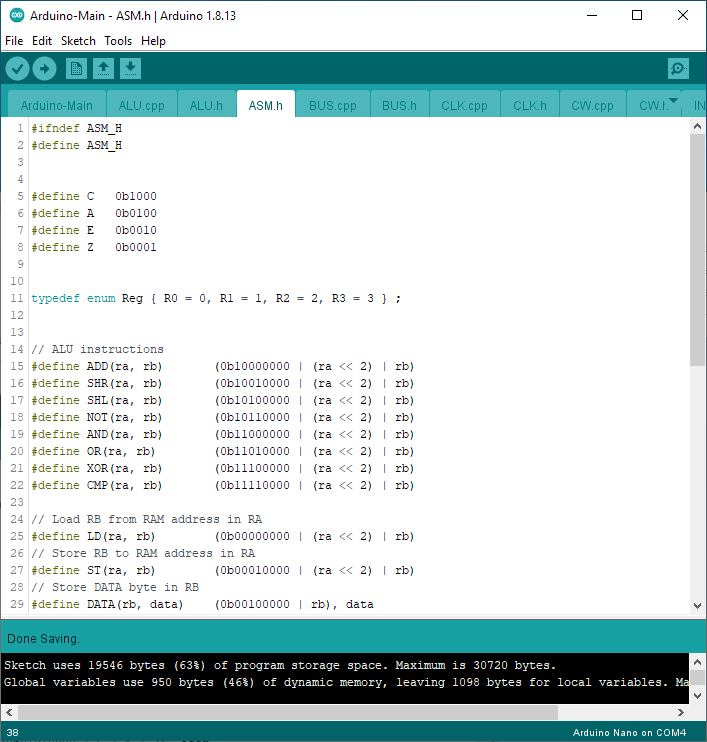
Videos/30- Assembly Language and Automatic Clock/asm1.png
