patrickleboutillier/jcscpu-hmc/Videos/6- The Register/Register_bb_testbench.png

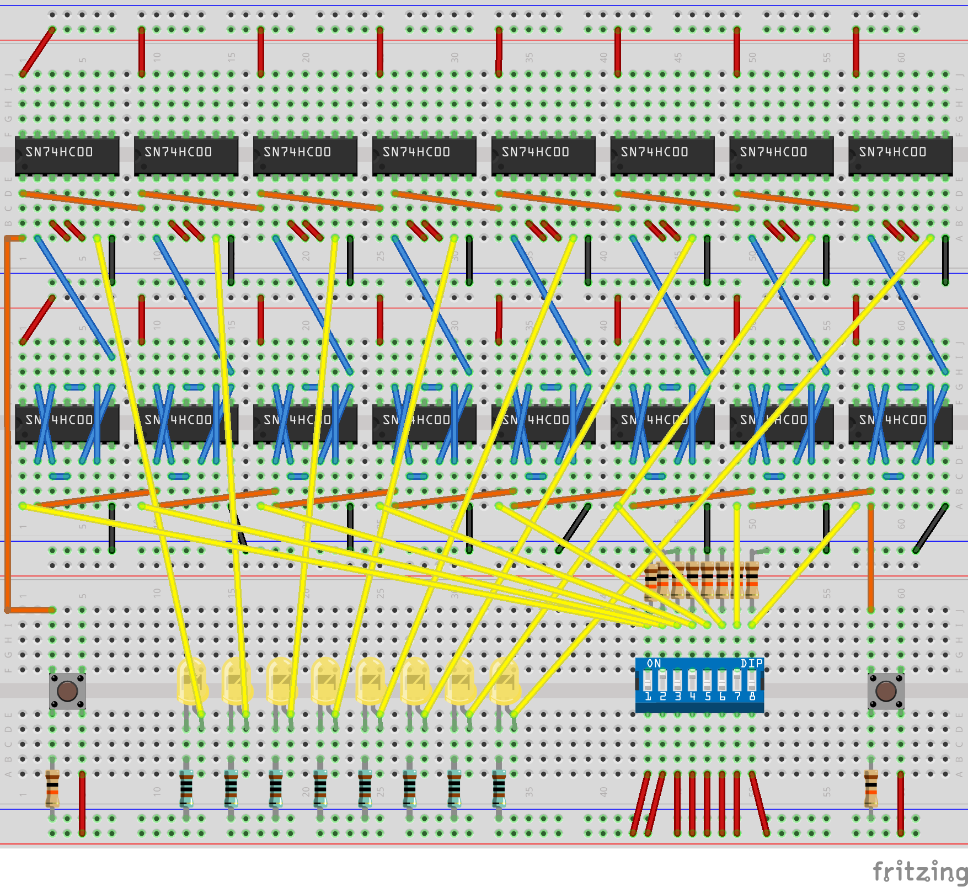
Videos/6- The Register/Register_bb_testbench.png
