patrickleboutillier/jcscpu-hmc/Arduino-Main/MICROCODE.h

/*
 * Microcode dispatch table.
 * This file was generated on Tue Nov 24 20:13:03 2020 by ..\genmc.pl.  
 */

#ifndef MICROCODE_h
#define MICROCODE_h

#define HLT       0b10000000000000000000000000000000
#define MAR_s     0b01000000000000000000000000000000
#define RAM_e     0b00100000000000000000000000000000
#define RAM_s     0b00010000000000000000000000000000
// #define X      0b00001000000000000000000000000000
#define ALU2      0b00000100000000000000000000000000
#define ALU1      0b00000010000000000000000000000000
#define ALU0      0b00000001000000000000000000000000

#define TMP_s     0b00000000100000000000000000000000
#define ACC_e     0b00000000010000000000000000000000
#define ACC_s     0b00000000001000000000000000000000
#define BUS1      0b00000000000100000000000000000000
#define FLAGS_s   0b00000000000010000000000000000000
#define Ctmp_e    0b00000000000001000000000000000000
#define IAR_e     0b00000000000000100000000000000000
// #define X      0b00000000000000010000000000000000

#define IO_s      0b00000000000000001000000000000000
#define IO_e      0b00000000000000000100000000000000
#define IO_io     0b00000000000000000010000000000000
#define IO_da     0b00000000000000000001000000000000
#define R0_e      0b00000000000000000000100000000000
#define R1_e      0b00000000000000000000010000000000
#define R0_s      0b00000000000000000000001000000000
#define R1_s      0b00000000000000000000000100000000

// #define X      0b00000000000000000000000010000000
#define JCOND     0b00000000000000000000000001000000
#define IAR_s     0b00000000000000000000000000100000
#define R2_e      0b00000000000000000000000000010000
#define R3_e      0b00000000000000000000000000001000
#define R2_s      0b00000000000000000000000000000100
#define R3_s      0b00000000000000000000000000000010
#define IR_s      0b00000000000000000000000000000001


PROGMEM const unsigned long microcode[] = {
  /* Entry    0 (inst*6+((step-4)*2)+clk) ->    LD:00000000@4e  */    R0_e,
  /* Entry    1 (inst*6+((step-4)*2)+clk) ->    LD:00000000@4s  */    MAR_s,
  /* Entry    2 (inst*6+((step-4)*2)+clk) ->    LD:00000000@5e  */    RAM_e,
  /* Entry    3 (inst*6+((step-4)*2)+clk) ->    LD:00000000@5s  */    R0_s,
  /* Entry    4 (inst*6+((step-4)*2)+clk) ->    LD:00000000@6e  */    0,
  /* Entry    5 (inst*6+((step-4)*2)+clk) ->    LD:00000000@6s  */    0,
  /* Entry    6 (inst*6+((step-4)*2)+clk) ->    LD:00000001@4e  */    R0_e,
  /* Entry    7 (inst*6+((step-4)*2)+clk) ->    LD:00000001@4s  */    MAR_s,
  /* Entry    8 (inst*6+((step-4)*2)+clk) ->    LD:00000001@5e  */    RAM_e,
  /* Entry    9 (inst*6+((step-4)*2)+clk) ->    LD:00000001@5s  */    R1_s,
  /* Entry   10 (inst*6+((step-4)*2)+clk) ->    LD:00000001@6e  */    0,
  /* Entry   11 (inst*6+((step-4)*2)+clk) ->    LD:00000001@6s  */    0,
  /* Entry   12 (inst*6+((step-4)*2)+clk) ->    LD:00000010@4e  */    R0_e,
  /* Entry   13 (inst*6+((step-4)*2)+clk) ->    LD:00000010@4s  */    MAR_s,
  /* Entry   14 (inst*6+((step-4)*2)+clk) ->    LD:00000010@5e  */    RAM_e,
  /* Entry   15 (inst*6+((step-4)*2)+clk) ->    LD:00000010@5s  */    R2_s,
  /* Entry   16 (inst*6+((step-4)*2)+clk) ->    LD:00000010@6e  */    0,
  /* Entry   17 (inst*6+((step-4)*2)+clk) ->    LD:00000010@6s  */    0,
  /* Entry   18 (inst*6+((step-4)*2)+clk) ->    LD:00000011@4e  */    R0_e,
  /* Entry   19 (inst*6+((step-4)*2)+clk) ->    LD:00000011@4s  */    MAR_s,
  /* Entry   20 (inst*6+((step-4)*2)+clk) ->    LD:00000011@5e  */    RAM_e,
  /* Entry   21 (inst*6+((step-4)*2)+clk) ->    LD:00000011@5s  */    R3_s,
  /* Entry   22 (inst*6+((step-4)*2)+clk) ->    LD:00000011@6e  */    0,
  /* Entry   23 (inst*6+((step-4)*2)+clk) ->    LD:00000011@6s  */    0,
  /* Entry   24 (inst*6+((step-4)*2)+clk) ->    LD:00000100@4e  */    R1_e,
  /* Entry   25 (inst*6+((step-4)*2)+clk) ->    LD:00000100@4s  */    MAR_s,
  /* Entry   26 (inst*6+((step-4)*2)+clk) ->    LD:00000100@5e  */    RAM_e,
  /* Entry   27 (inst*6+((step-4)*2)+clk) ->    LD:00000100@5s  */    R0_s,
  /* Entry   28 (inst*6+((step-4)*2)+clk) ->    LD:00000100@6e  */    0,
  /* Entry   29 (inst*6+((step-4)*2)+clk) ->    LD:00000100@6s  */    0,
  /* Entry   30 (inst*6+((step-4)*2)+clk) ->    LD:00000101@4e  */    R1_e,
  /* Entry   31 (inst*6+((step-4)*2)+clk) ->    LD:00000101@4s  */    MAR_s,
  /* Entry   32 (inst*6+((step-4)*2)+clk) ->    LD:00000101@5e  */    RAM_e,
  /* Entry   33 (inst*6+((step-4)*2)+clk) ->    LD:00000101@5s  */    R1_s,
  /* Entry   34 (inst*6+((step-4)*2)+clk) ->    LD:00000101@6e  */    0,
  /* Entry   35 (inst*6+((step-4)*2)+clk) ->    LD:00000101@6s  */    0,
  /* Entry   36 (inst*6+((step-4)*2)+clk) ->    LD:00000110@4e  */    R1_e,
  /* Entry   37 (inst*6+((step-4)*2)+clk) ->    LD:00000110@4s  */    MAR_s,
  /* Entry   38 (inst*6+((step-4)*2)+clk) ->    LD:00000110@5e  */    RAM_e,
  /* Entry   39 (inst*6+((step-4)*2)+clk) ->    LD:00000110@5s  */    R2_s,
  /* Entry   40 (inst*6+((step-4)*2)+clk) ->    LD:00000110@6e  */    0,
  /* Entry   41 (inst*6+((step-4)*2)+clk) ->    LD:00000110@6s  */    0,
  /* Entry   42 (inst*6+((step-4)*2)+clk) ->    LD:00000111@4e  */    R1_e,
  /* Entry   43 (inst*6+((step-4)*2)+clk) ->    LD:00000111@4s  */    MAR_s,
  /* Entry   44 (inst*6+((step-4)*2)+clk) ->    LD:00000111@5e  */    RAM_e,
  /* Entry   45 (inst*6+((step-4)*2)+clk) ->    LD:00000111@5s  */    R3_s,
  /* Entry   46 (inst*6+((step-4)*2)+clk) ->    LD:00000111@6e  */    0,
  /* Entry   47 (inst*6+((step-4)*2)+clk) ->    LD:00000111@6s  */    0,
  /* Entry   48 (inst*6+((step-4)*2)+clk) ->    LD:00001000@4e  */    R2_e,
  /* Entry   49 (inst*6+((step-4)*2)+clk) ->    LD:00001000@4s  */    MAR_s,
  /* Entry   50 (inst*6+((step-4)*2)+clk) ->    LD:00001000@5e  */    RAM_e,
  /* Entry   51 (inst*6+((step-4)*2)+clk) ->    LD:00001000@5s  */    R0_s,
  /* Entry   52 (inst*6+((step-4)*2)+clk) ->    LD:00001000@6e  */    0,
  /* Entry   53 (inst*6+((step-4)*2)+clk) ->    LD:00001000@6s  */    0,
  /* Entry   54 (inst*6+((step-4)*2)+clk) ->    LD:00001001@4e  */    R2_e,
  /* Entry   55 (inst*6+((step-4)*2)+clk) ->    LD:00001001@4s  */    MAR_s,
  /* Entry   56 (inst*6+((step-4)*2)+clk) ->    LD:00001001@5e  */    RAM_e,
  /* Entry   57 (inst*6+((step-4)*2)+clk) ->    LD:00001001@5s  */    R1_s,
  /* Entry   58 (inst*6+((step-4)*2)+clk) ->    LD:00001001@6e  */    0,
  /* Entry   59 (inst*6+((step-4)*2)+clk) ->    LD:00001001@6s  */    0,
  /* Entry   60 (inst*6+((step-4)*2)+clk) ->    LD:00001010@4e  */    R2_e,
  /* Entry   61 (inst*6+((step-4)*2)+clk) ->    LD:00001010@4s  */    MAR_s,
  /* Entry   62 (inst*6+((step-4)*2)+clk) ->    LD:00001010@5e  */    RAM_e,
  /* Entry   63 (inst*6+((step-4)*2)+clk) ->    LD:00001010@5s  */    R2_s,
  /* Entry   64 (inst*6+((step-4)*2)+clk) ->    LD:00001010@6e  */    0,
  /* Entry   65 (inst*6+((step-4)*2)+clk) ->    LD:00001010@6s  */    0,
  /* Entry   66 (inst*6+((step-4)*2)+clk) ->    LD:00001011@4e  */    R2_e,
  /* Entry   67 (inst*6+((step-4)*2)+clk) ->    LD:00001011@4s  */    MAR_s,
  /* Entry   68 (inst*6+((step-4)*2)+clk) ->    LD:00001011@5e  */    RAM_e,
  /* Entry   69 (inst*6+((step-4)*2)+clk) ->    LD:00001011@5s  */    R3_s,
  /* Entry   70 (inst*6+((step-4)*2)+clk) ->    LD:00001011@6e  */    0,
  /* Entry   71 (inst*6+((step-4)*2)+clk) ->    LD:00001011@6s  */    0,
  /* Entry   72 (inst*6+((step-4)*2)+clk) ->    LD:00001100@4e  */    R3_e,
  /* Entry   73 (inst*6+((step-4)*2)+clk) ->    LD:00001100@4s  */    MAR_s,
  /* Entry   74 (inst*6+((step-4)*2)+clk) ->    LD:00001100@5e  */    RAM_e,
  /* Entry   75 (inst*6+((step-4)*2)+clk) ->    LD:00001100@5s  */    R0_s,
  /* Entry   76 (inst*6+((step-4)*2)+clk) ->    LD:00001100@6e  */    0,
  /* Entry   77 (inst*6+((step-4)*2)+clk) ->    LD:00001100@6s  */    0,
  /* Entry   78 (inst*6+((step-4)*2)+clk) ->    LD:00001101@4e  */    R3_e,
  /* Entry   79 (inst*6+((step-4)*2)+clk) ->    LD:00001101@4s  */    MAR_s,
  /* Entry   80 (inst*6+((step-4)*2)+clk) ->    LD:00001101@5e  */    RAM_e,
  /* Entry   81 (inst*6+((step-4)*2)+clk) ->    LD:00001101@5s  */    R1_s,
  /* Entry   82 (inst*6+((step-4)*2)+clk) ->    LD:00001101@6e  */    0,
  /* Entry   83 (inst*6+((step-4)*2)+clk) ->    LD:00001101@6s  */    0,
  /* Entry   84 (inst*6+((step-4)*2)+clk) ->    LD:00001110@4e  */    R3_e,
  /* Entry   85 (inst*6+((step-4)*2)+clk) ->    LD:00001110@4s  */    MAR_s,
  /* Entry   86 (inst*6+((step-4)*2)+clk) ->    LD:00001110@5e  */    RAM_e,
  /* Entry   87 (inst*6+((step-4)*2)+clk) ->    LD:00001110@5s  */    R2_s,
  /* Entry   88 (inst*6+((step-4)*2)+clk) ->    LD:00001110@6e  */    0,
  /* Entry   89 (inst*6+((step-4)*2)+clk) ->    LD:00001110@6s  */    0,
  /* Entry   90 (inst*6+((step-4)*2)+clk) ->    LD:00001111@4e  */    R3_e,
  /* Entry   91 (inst*6+((step-4)*2)+clk) ->    LD:00001111@4s  */    MAR_s,
  /* Entry   92 (inst*6+((step-4)*2)+clk) ->    LD:00001111@5e  */    RAM_e,
  /* Entry   93 (inst*6+((step-4)*2)+clk) ->    LD:00001111@5s  */    R3_s,
  /* Entry   94 (inst*6+((step-4)*2)+clk) ->    LD:00001111@6e  */    0,
  /* Entry   95 (inst*6+((step-4)*2)+clk) ->    LD:00001111@6s  */    0,
  /* Entry   96 (inst*6+((step-4)*2)+clk) ->    ST:00010000@4e  */    R0_e,
  /* Entry   97 (inst*6+((step-4)*2)+clk) ->    ST:00010000@4s  */    MAR_s,
  /* Entry   98 (inst*6+((step-4)*2)+clk) ->    ST:00010000@5e  */    R0_e,
  /* Entry   99 (inst*6+((step-4)*2)+clk) ->    ST:00010000@5s  */    RAM_s,
  /* Entry  100 (inst*6+((step-4)*2)+clk) ->    ST:00010000@6e  */    0,
  /* Entry  101 (inst*6+((step-4)*2)+clk) ->    ST:00010000@6s  */    0,
  /* Entry  102 (inst*6+((step-4)*2)+clk) ->    ST:00010001@4e  */    R0_e,
  /* Entry  103 (inst*6+((step-4)*2)+clk) ->    ST:00010001@4s  */    MAR_s,
  /* Entry  104 (inst*6+((step-4)*2)+clk) ->    ST:00010001@5e  */    R1_e,
  /* Entry  105 (inst*6+((step-4)*2)+clk) ->    ST:00010001@5s  */    RAM_s,
  /* Entry  106 (inst*6+((step-4)*2)+clk) ->    ST:00010001@6e  */    0,
  /* Entry  107 (inst*6+((step-4)*2)+clk) ->    ST:00010001@6s  */    0,
  /* Entry  108 (inst*6+((step-4)*2)+clk) ->    ST:00010010@4e  */    R0_e,
  /* Entry  109 (inst*6+((step-4)*2)+clk) ->    ST:00010010@4s  */    MAR_s,
  /* Entry  110 (inst*6+((step-4)*2)+clk) ->    ST:00010010@5e  */    R2_e,
  /* Entry  111 (inst*6+((step-4)*2)+clk) ->    ST:00010010@5s  */    RAM_s,
  /* Entry  112 (inst*6+((step-4)*2)+clk) ->    ST:00010010@6e  */    0,
  /* Entry  113 (inst*6+((step-4)*2)+clk) ->    ST:00010010@6s  */    0,
  /* Entry  114 (inst*6+((step-4)*2)+clk) ->    ST:00010011@4e  */    R0_e,
  /* Entry  115 (inst*6+((step-4)*2)+clk) ->    ST:00010011@4s  */    MAR_s,
  /* Entry  116 (inst*6+((step-4)*2)+clk) ->    ST:00010011@5e  */    R3_e,
  /* Entry  117 (inst*6+((step-4)*2)+clk) ->    ST:00010011@5s  */    RAM_s,
  /* Entry  118 (inst*6+((step-4)*2)+clk) ->    ST:00010011@6e  */    0,
  /* Entry  119 (inst*6+((step-4)*2)+clk) ->    ST:00010011@6s  */    0,
  /* Entry  120 (inst*6+((step-4)*2)+clk) ->    ST:00010100@4e  */    R1_e,
  /* Entry  121 (inst*6+((step-4)*2)+clk) ->    ST:00010100@4s  */    MAR_s,
  /* Entry  122 (inst*6+((step-4)*2)+clk) ->    ST:00010100@5e  */    R0_e,
  /* Entry  123 (inst*6+((step-4)*2)+clk) ->    ST:00010100@5s  */    RAM_s,
  /* Entry  124 (inst*6+((step-4)*2)+clk) ->    ST:00010100@6e  */    0,
  /* Entry  125 (inst*6+((step-4)*2)+clk) ->    ST:00010100@6s  */    0,
  /* Entry  126 (inst*6+((step-4)*2)+clk) ->    ST:00010101@4e  */    R1_e,
  /* Entry  127 (inst*6+((step-4)*2)+clk) ->    ST:00010101@4s  */    MAR_s,
  /* Entry  128 (inst*6+((step-4)*2)+clk) ->    ST:00010101@5e  */    R1_e,
  /* Entry  129 (inst*6+((step-4)*2)+clk) ->    ST:00010101@5s  */    RAM_s,
  /* Entry  130 (inst*6+((step-4)*2)+clk) ->    ST:00010101@6e  */    0,
  /* Entry  131 (inst*6+((step-4)*2)+clk) ->    ST:00010101@6s  */    0,
  /* Entry  132 (inst*6+((step-4)*2)+clk) ->    ST:00010110@4e  */    R1_e,
  /* Entry  133 (inst*6+((step-4)*2)+clk) ->    ST:00010110@4s  */    MAR_s,
  /* Entry  134 (inst*6+((step-4)*2)+clk) ->    ST:00010110@5e  */    R2_e,
  /* Entry  135 (inst*6+((step-4)*2)+clk) ->    ST:00010110@5s  */    RAM_s,
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
  /* Entry  558 (inst*6+((step-4)*2)+clk) -> JCOND:01011101@4e  */    BUS1|IAR_e,
  /* Entry  559 (inst*6+((step-4)*2)+clk) -> JCOND:01011101@4s  */    MAR_s|ACC_s,
  /* Entry  560 (inst*6+((step-4)*2)+clk) -> JCOND:01011101@5e  */    ACC_e,
  /* Entry  561 (inst*6+((step-4)*2)+clk) -> JCOND:01011101@5s  */    IAR_s,
  /* Entry  562 (inst*6+((step-4)*2)+clk) -> JCOND:01011101@6e  */    RAM_e,
  /* Entry  563 (inst*6+((step-4)*2)+clk) -> JCOND:01011101@6s  */    JCOND,
  /* Entry  564 (inst*6+((step-4)*2)+clk) -> JCOND:01011110@4e  */    BUS1|IAR_e,
  /* Entry  565 (inst*6+((step-4)*2)+clk) -> JCOND:01011110@4s  */    MAR_s|ACC_s,
  /* Entry  566 (inst*6+((step-4)*2)+clk) -> JCOND:01011110@5e  */    ACC_e,
  /* Entry  567 (inst*6+((step-4)*2)+clk) -> JCOND:01011110@5s  */    IAR_s,
  /* Entry  568 (inst*6+((step-4)*2)+clk) -> JCOND:01011110@6e  */    RAM_e,
  /* Entry  569 (inst*6+((step-4)*2)+clk) -> JCOND:01011110@6s  */    JCOND,
  /* Entry  570 (inst*6+((step-4)*2)+clk) -> JCOND:01011111@4e  */    BUS1|IAR_e,
  /* Entry  571 (inst*6+((step-4)*2)+clk) -> JCOND:01011111@4s  */    MAR_s|ACC_s,
  /* Entry  572 (inst*6+((step-4)*2)+clk) -> JCOND:01011111@5e  */    ACC_e,
  /* Entry  573 (inst*6+((step-4)*2)+clk) -> JCOND:01011111@5s  */    IAR_s,
  /* Entry  574 (inst*6+((step-4)*2)+clk) -> JCOND:01011111@6e  */    RAM_e,
  /* Entry  575 (inst*6+((step-4)*2)+clk) -> JCOND:01011111@6s  */    JCOND,
  /* Entry  576 (inst*6+((step-4)*2)+clk) ->   CLF:01100000@4e  */    BUS1,
  /* Entry  577 (inst*6+((step-4)*2)+clk) ->   CLF:01100000@4s  */    FLAGS_s,
  /* Entry  578 (inst*6+((step-4)*2)+clk) ->   CLF:01100000@5e  */    0,
  /* Entry  579 (inst*6+((step-4)*2)+clk) ->   CLF:01100000@5s  */    0,
  /* Entry  580 (inst*6+((step-4)*2)+clk) ->   CLF:01100000@6e  */    0,
  /* Entry  581 (inst*6+((step-4)*2)+clk) ->   CLF:01100000@6s  */    0,
  /* Entry  582 (inst*6+((step-4)*2)+clk) ->   CLF:01100001@4e  (Invalid instruction) */    0,
  /* Entry  583 (inst*6+((step-4)*2)+clk) ->   CLF:01100001@4s  (Invalid instruction) */    0,
  /* Entry  584 (inst*6+((step-4)*2)+clk) ->   CLF:01100001@5e  (Invalid instruction) */    0,
  /* Entry  585 (inst*6+((step-4)*2)+clk) ->   CLF:01100001@5s  (Invalid instruction) */    0,
  /* Entry  586 (inst*6+((step-4)*2)+clk) ->   CLF:01100001@6e  (Invalid instruction) */    0,
  /* Entry  587 (inst*6+((step-4)*2)+clk) ->   CLF:01100001@6s  (Invalid instruction) */    0,
  /* Entry  588 (inst*6+((step-4)*2)+clk) ->   CLF:01100010@4e  (Invalid instruction) */    0,
  /* Entry  589 (inst*6+((step-4)*2)+clk) ->   CLF:01100010@4s  (Invalid instruction) */    0,
  /* Entry  590 (inst*6+((step-4)*2)+clk) ->   CLF:01100010@5e  (Invalid instruction) */    0,
  /* Entry  591 (inst*6+((step-4)*2)+clk) ->   CLF:01100010@5s  (Invalid instruction) */    0,
  /* Entry  592 (inst*6+((step-4)*2)+clk) ->   CLF:01100010@6e  (Invalid instruction) */    0,
  /* Entry  593 (inst*6+((step-4)*2)+clk) ->   CLF:01100010@6s  (Invalid instruction) */    0,
  /* Entry  594 (inst*6+((step-4)*2)+clk) ->   CLF:01100011@4e  (Invalid instruction) */    0,
  /* Entry  595 (inst*6+((step-4)*2)+clk) ->   CLF:01100011@4s  (Invalid instruction) */    0,
  /* Entry  596 (inst*6+((step-4)*2)+clk) ->   CLF:01100011@5e  (Invalid instruction) */    0,
  /* Entry  597 (inst*6+((step-4)*2)+clk) ->   CLF:01100011@5s  (Invalid instruction) */    0,
  /* Entry  598 (inst*6+((step-4)*2)+clk) ->   CLF:01100011@6e  (Invalid instruction) */    0,
  /* Entry  599 (inst*6+((step-4)*2)+clk) ->   CLF:01100011@6s  (Invalid instruction) */    0,
  /* Entry  600 (inst*6+((step-4)*2)+clk) ->   CLF:01100100@4e  (Invalid instruction) */    0,
  /* Entry  601 (inst*6+((step-4)*2)+clk) ->   CLF:01100100@4s  (Invalid instruction) */    0,
  /* Entry  602 (inst*6+((step-4)*2)+clk) ->   CLF:01100100@5e  (Invalid instruction) */    0,
  /* Entry  603 (inst*6+((step-4)*2)+clk) ->   CLF:01100100@5s  (Invalid instruction) */    0,
  /* Entry  604 (inst*6+((step-4)*2)+clk) ->   CLF:01100100@6e  (Invalid instruction) */    0,
  /* Entry  605 (inst*6+((step-4)*2)+clk) ->   CLF:01100100@6s  (Invalid instruction) */    0,
  /* Entry  606 (inst*6+((step-4)*2)+clk) ->   CLF:01100101@4e  (Invalid instruction) */    0,
  /* Entry  607 (inst*6+((step-4)*2)+clk) ->   CLF:01100101@4s  (Invalid instruction) */    0,
  /* Entry  608 (inst*6+((step-4)*2)+clk) ->   CLF:01100101@5e  (Invalid instruction) */    0,
  /* Entry  609 (inst*6+((step-4)*2)+clk) ->   CLF:01100101@5s  (Invalid instruction) */    0,
  /* Entry  610 (inst*6+((step-4)*2)+clk) ->   CLF:01100101@6e  (Invalid instruction) */    0,
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
  /* Entry  732 (inst*6+((step-4)*2)+clk) ->    IO:01111010@4e  */    R2_e|IO_io,
  /* Entry  733 (inst*6+((step-4)*2)+clk) ->    IO:01111010@4s  */    IO_s|IO_io,
  /* Entry  734 (inst*6+((step-4)*2)+clk) ->    IO:01111010@5e  */    IO_io,
  /* Entry  735 (inst*6+((step-4)*2)+clk) ->    IO:01111010@5s  */    IO_io,
  /* Entry  736 (inst*6+((step-4)*2)+clk) ->    IO:01111010@6e  */    0,
  /* Entry  737 (inst*6+((step-4)*2)+clk) ->    IO:01111010@6s  */    0,
  /* Entry  738 (inst*6+((step-4)*2)+clk) ->    IO:01111011@4e  */    R3_e|IO_io,
  /* Entry  739 (inst*6+((step-4)*2)+clk) ->    IO:01111011@4s  */    IO_s|IO_io,
  /* Entry  740 (inst*6+((step-4)*2)+clk) ->    IO:01111011@5e  */    IO_io,
  /* Entry  741 (inst*6+((step-4)*2)+clk) ->    IO:01111011@5s  */    IO_io,
  /* Entry  742 (inst*6+((step-4)*2)+clk) ->    IO:01111011@6e  */    0,
  /* Entry  743 (inst*6+((step-4)*2)+clk) ->    IO:01111011@6s  */    0,
  /* Entry  744 (inst*6+((step-4)*2)+clk) ->    IO:01111100@4e  */    R0_e|IO_io|IO_da,
  /* Entry  745 (inst*6+((step-4)*2)+clk) ->    IO:01111100@4s  */    IO_s|IO_io|IO_da,
  /* Entry  746 (inst*6+((step-4)*2)+clk) ->    IO:01111100@5e  */    IO_io|IO_da,
  /* Entry  747 (inst*6+((step-4)*2)+clk) ->    IO:01111100@5s  */    IO_io|IO_da,
  /* Entry  748 (inst*6+((step-4)*2)+clk) ->    IO:01111100@6e  */    0,
  /* Entry  749 (inst*6+((step-4)*2)+clk) ->    IO:01111100@6s  */    0,
  /* Entry  750 (inst*6+((step-4)*2)+clk) ->    IO:01111101@4e  */    R1_e|IO_io|IO_da,
  /* Entry  751 (inst*6+((step-4)*2)+clk) ->    IO:01111101@4s  */    IO_s|IO_io|IO_da,
  /* Entry  752 (inst*6+((step-4)*2)+clk) ->    IO:01111101@5e  */    IO_io|IO_da,
  /* Entry  753 (inst*6+((step-4)*2)+clk) ->    IO:01111101@5s  */    IO_io|IO_da,
  /* Entry  754 (inst*6+((step-4)*2)+clk) ->    IO:01111101@6e  */    0,
  /* Entry  755 (inst*6+((step-4)*2)+clk) ->    IO:01111101@6s  */    0,
  /* Entry  756 (inst*6+((step-4)*2)+clk) ->    IO:01111110@4e  */    R2_e|IO_io|IO_da,
  /* Entry  757 (inst*6+((step-4)*2)+clk) ->    IO:01111110@4s  */    IO_s|IO_io|IO_da,
  /* Entry  758 (inst*6+((step-4)*2)+clk) ->    IO:01111110@5e  */    IO_io|IO_da,
  /* Entry  759 (inst*6+((step-4)*2)+clk) ->    IO:01111110@5s  */    IO_io|IO_da,
  /* Entry  760 (inst*6+((step-4)*2)+clk) ->    IO:01111110@6e  */    0,
  /* Entry  761 (inst*6+((step-4)*2)+clk) ->    IO:01111110@6s  */    0,
  /* Entry  762 (inst*6+((step-4)*2)+clk) ->    IO:01111111@4e  */    R3_e|IO_io|IO_da,
  /* Entry  763 (inst*6+((step-4)*2)+clk) ->    IO:01111111@4s  */    IO_s|IO_io|IO_da,
  /* Entry  764 (inst*6+((step-4)*2)+clk) ->    IO:01111111@5e  */    IO_io|IO_da,
  /* Entry  765 (inst*6+((step-4)*2)+clk) ->    IO:01111111@5s  */    IO_io|IO_da,
  /* Entry  766 (inst*6+((step-4)*2)+clk) ->    IO:01111111@6e  */    0,
  /* Entry  767 (inst*6+((step-4)*2)+clk) ->    IO:01111111@6s  */    0,
  /* Entry  768 (inst*6+((step-4)*2)+clk) ->   ADD:10000000@4e  */    R0_e,
  /* Entry  769 (inst*6+((step-4)*2)+clk) ->   ADD:10000000@4s  */    TMP_s,
  /* Entry  770 (inst*6+((step-4)*2)+clk) ->   ADD:10000000@5e  */    R0_e|Ctmp_e,
  /* Entry  771 (inst*6+((step-4)*2)+clk) ->   ADD:10000000@5s  */    ACC_s|FLAGS_s,
  /* Entry  772 (inst*6+((step-4)*2)+clk) ->   ADD:10000000@6e  */    ACC_e,
  /* Entry  773 (inst*6+((step-4)*2)+clk) ->   ADD:10000000@6s  */    R0_s,
  /* Entry  774 (inst*6+((step-4)*2)+clk) ->   ADD:10000001@4e  */    R1_e,
  /* Entry  775 (inst*6+((step-4)*2)+clk) ->   ADD:10000001@4s  */    TMP_s,
  /* Entry  776 (inst*6+((step-4)*2)+clk) ->   ADD:10000001@5e  */    R0_e|Ctmp_e,
  /* Entry  777 (inst*6+((step-4)*2)+clk) ->   ADD:10000001@5s  */    ACC_s|FLAGS_s,
  /* Entry  778 (inst*6+((step-4)*2)+clk) ->   ADD:10000001@6e  */    ACC_e,
  /* Entry  779 (inst*6+((step-4)*2)+clk) ->   ADD:10000001@6s  */    R1_s,
  /* Entry  780 (inst*6+((step-4)*2)+clk) ->   ADD:10000010@4e  */    R2_e,
  /* Entry  781 (inst*6+((step-4)*2)+clk) ->   ADD:10000010@4s  */    TMP_s,
  /* Entry  782 (inst*6+((step-4)*2)+clk) ->   ADD:10000010@5e  */    R0_e|Ctmp_e,
  /* Entry  783 (inst*6+((step-4)*2)+clk) ->   ADD:10000010@5s  */    ACC_s|FLAGS_s,
  /* Entry  784 (inst*6+((step-4)*2)+clk) ->   ADD:10000010@6e  */    ACC_e,
  /* Entry  785 (inst*6+((step-4)*2)+clk) ->   ADD:10000010@6s  */    R2_s,
  /* Entry  786 (inst*6+((step-4)*2)+clk) ->   ADD:10000011@4e  */    R3_e,
  /* Entry  787 (inst*6+((step-4)*2)+clk) ->   ADD:10000011@4s  */    TMP_s,
  /* Entry  788 (inst*6+((step-4)*2)+clk) ->   ADD:10000011@5e  */    R0_e|Ctmp_e,
  /* Entry  789 (inst*6+((step-4)*2)+clk) ->   ADD:10000011@5s  */    ACC_s|FLAGS_s,
  /* Entry  790 (inst*6+((step-4)*2)+clk) ->   ADD:10000011@6e  */    ACC_e,
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
  /* Entry  845 (inst*6+((step-4)*2)+clk) ->   ADD:10001100@6s  */    R0_s,
  /* Entry  846 (inst*6+((step-4)*2)+clk) ->   ADD:10001101@4e  */    R1_e,
  /* Entry  847 (inst*6+((step-4)*2)+clk) ->   ADD:10001101@4s  */    TMP_s,
  /* Entry  848 (inst*6+((step-4)*2)+clk) ->   ADD:10001101@5e  */    R3_e|Ctmp_e,
  /* Entry  849 (inst*6+((step-4)*2)+clk) ->   ADD:10001101@5s  */    ACC_s|FLAGS_s,
  /* Entry  850 (inst*6+((step-4)*2)+clk) ->   ADD:10001101@6e  */    ACC_e,
  /* Entry  851 (inst*6+((step-4)*2)+clk) ->   ADD:10001101@6s  */    R1_s,
  /* Entry  852 (inst*6+((step-4)*2)+clk) ->   ADD:10001110@4e  */    R2_e,
  /* Entry  853 (inst*6+((step-4)*2)+clk) ->   ADD:10001110@4s  */    TMP_s,
  /* Entry  854 (inst*6+((step-4)*2)+clk) ->   ADD:10001110@5e  */    R3_e|Ctmp_e,
  /* Entry  855 (inst*6+((step-4)*2)+clk) ->   ADD:10001110@5s  */    ACC_s|FLAGS_s,
  /* Entry  856 (inst*6+((step-4)*2)+clk) ->   ADD:10001110@6e  */    ACC_e,
  /* Entry  857 (inst*6+((step-4)*2)+clk) ->   ADD:10001110@6s  */    R2_s,
  /* Entry  858 (inst*6+((step-4)*2)+clk) ->   ADD:10001111@4e  */    R3_e,
  /* Entry  859 (inst*6+((step-4)*2)+clk) ->   ADD:10001111@4s  */    TMP_s,
  /* Entry  860 (inst*6+((step-4)*2)+clk) ->   ADD:10001111@5e  */    R3_e|Ctmp_e,
  /* Entry  861 (inst*6+((step-4)*2)+clk) ->   ADD:10001111@5s  */    ACC_s|FLAGS_s,
  /* Entry  862 (inst*6+((step-4)*2)+clk) ->   ADD:10001111@6e  */    ACC_e,
  /* Entry  863 (inst*6+((step-4)*2)+clk) ->   ADD:10001111@6s  */    R3_s,
  /* Entry  864 (inst*6+((step-4)*2)+clk) ->   SHR:10010000@4e  */    ALU0|R0_e,
  /* Entry  865 (inst*6+((step-4)*2)+clk) ->   SHR:10010000@4s  */    ALU0|TMP_s,
  /* Entry  866 (inst*6+((step-4)*2)+clk) ->   SHR:10010000@5e  */    ALU0|R0_e|Ctmp_e,
  /* Entry  867 (inst*6+((step-4)*2)+clk) ->   SHR:10010000@5s  */    ALU0|ACC_s|FLAGS_s,
  /* Entry  868 (inst*6+((step-4)*2)+clk) ->   SHR:10010000@6e  */    ALU0|ACC_e,
  /* Entry  869 (inst*6+((step-4)*2)+clk) ->   SHR:10010000@6s  */    R0_s,
  /* Entry  870 (inst*6+((step-4)*2)+clk) ->   SHR:10010001@4e  */    ALU0|R1_e,
  /* Entry  871 (inst*6+((step-4)*2)+clk) ->   SHR:10010001@4s  */    ALU0|TMP_s,
  /* Entry  872 (inst*6+((step-4)*2)+clk) ->   SHR:10010001@5e  */    ALU0|R0_e|Ctmp_e,
  /* Entry  873 (inst*6+((step-4)*2)+clk) ->   SHR:10010001@5s  */    ALU0|ACC_s|FLAGS_s,
  /* Entry  874 (inst*6+((step-4)*2)+clk) ->   SHR:10010001@6e  */    ALU0|ACC_e,
  /* Entry  875 (inst*6+((step-4)*2)+clk) ->   SHR:10010001@6s  */    R1_s,
  /* Entry  876 (inst*6+((step-4)*2)+clk) ->   SHR:10010010@4e  */    ALU0|R2_e,
  /* Entry  877 (inst*6+((step-4)*2)+clk) ->   SHR:10010010@4s  */    ALU0|TMP_s,
  /* Entry  878 (inst*6+((step-4)*2)+clk) ->   SHR:10010010@5e  */    ALU0|R0_e|Ctmp_e,
  /* Entry  879 (inst*6+((step-4)*2)+clk) ->   SHR:10010010@5s  */    ALU0|ACC_s|FLAGS_s,
  /* Entry  880 (inst*6+((step-4)*2)+clk) ->   SHR:10010010@6e  */    ALU0|ACC_e,
  /* Entry  881 (inst*6+((step-4)*2)+clk) ->   SHR:10010010@6s  */    R2_s,
  /* Entry  882 (inst*6+((step-4)*2)+clk) ->   SHR:10010011@4e  */    ALU0|R3_e,
  /* Entry  883 (inst*6+((step-4)*2)+clk) ->   SHR:10010011@4s  */    ALU0|TMP_s,
  /* Entry  884 (inst*6+((step-4)*2)+clk) ->   SHR:10010011@5e  */    ALU0|R0_e|Ctmp_e,
  /* Entry  885 (inst*6+((step-4)*2)+clk) ->   SHR:10010011@5s  */    ALU0|ACC_s|FLAGS_s,
  /* Entry  886 (inst*6+((step-4)*2)+clk) ->   SHR:10010011@6e  */    ALU0|ACC_e,
  /* Entry  887 (inst*6+((step-4)*2)+clk) ->   SHR:10010011@6s  */    R3_s,
  /* Entry  888 (inst*6+((step-4)*2)+clk) ->   SHR:10010100@4e  */    ALU0|R0_e,
  /* Entry  889 (inst*6+((step-4)*2)+clk) ->   SHR:10010100@4s  */    ALU0|TMP_s,
  /* Entry  890 (inst*6+((step-4)*2)+clk) ->   SHR:10010100@5e  */    ALU0|R1_e|Ctmp_e,
  /* Entry  891 (inst*6+((step-4)*2)+clk) ->   SHR:10010100@5s  */    ALU0|ACC_s|FLAGS_s,
  /* Entry  892 (inst*6+((step-4)*2)+clk) ->   SHR:10010100@6e  */    ALU0|ACC_e,
  /* Entry  893 (inst*6+((step-4)*2)+clk) ->   SHR:10010100@6s  */    R0_s,
  /* Entry  894 (inst*6+((step-4)*2)+clk) ->   SHR:10010101@4e  */    ALU0|R1_e,
  /* Entry  895 (inst*6+((step-4)*2)+clk) ->   SHR:10010101@4s  */    ALU0|TMP_s,
  /* Entry  896 (inst*6+((step-4)*2)+clk) ->   SHR:10010101@5e  */    ALU0|R1_e|Ctmp_e,
  /* Entry  897 (inst*6+((step-4)*2)+clk) ->   SHR:10010101@5s  */    ALU0|ACC_s|FLAGS_s,
  /* Entry  898 (inst*6+((step-4)*2)+clk) ->   SHR:10010101@6e  */    ALU0|ACC_e,
  /* Entry  899 (inst*6+((step-4)*2)+clk) ->   SHR:10010101@6s  */    R1_s,
  /* Entry  900 (inst*6+((step-4)*2)+clk) ->   SHR:10010110@4e  */    ALU0|R2_e,
  /* Entry  901 (inst*6+((step-4)*2)+clk) ->   SHR:10010110@4s  */    ALU0|TMP_s,
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
  /* Entry  989 (inst*6+((step-4)*2)+clk) ->   SHL:10100100@6s  */    R0_s,
  /* Entry  990 (inst*6+((step-4)*2)+clk) ->   SHL:10100101@4e  */    ALU1|R1_e,
  /* Entry  991 (inst*6+((step-4)*2)+clk) ->   SHL:10100101@4s  */    ALU1|TMP_s,
  /* Entry  992 (inst*6+((step-4)*2)+clk) ->   SHL:10100101@5e  */    ALU1|R1_e|Ctmp_e,
  /* Entry  993 (inst*6+((step-4)*2)+clk) ->   SHL:10100101@5s  */    ALU1|ACC_s|FLAGS_s,
  /* Entry  994 (inst*6+((step-4)*2)+clk) ->   SHL:10100101@6e  */    ALU1|ACC_e,
  /* Entry  995 (inst*6+((step-4)*2)+clk) ->   SHL:10100101@6s  */    R1_s,
  /* Entry  996 (inst*6+((step-4)*2)+clk) ->   SHL:10100110@4e  */    ALU1|R2_e,
  /* Entry  997 (inst*6+((step-4)*2)+clk) ->   SHL:10100110@4s  */    ALU1|TMP_s,
  /* Entry  998 (inst*6+((step-4)*2)+clk) ->   SHL:10100110@5e  */    ALU1|R1_e|Ctmp_e,
  /* Entry  999 (inst*6+((step-4)*2)+clk) ->   SHL:10100110@5s  */    ALU1|ACC_s|FLAGS_s,
  /* Entry 1000 (inst*6+((step-4)*2)+clk) ->   SHL:10100110@6e  */    ALU1|ACC_e,
  /* Entry 1001 (inst*6+((step-4)*2)+clk) ->   SHL:10100110@6s  */    R2_s,
  /* Entry 1002 (inst*6+((step-4)*2)+clk) ->   SHL:10100111@4e  */    ALU1|R3_e,
  /* Entry 1003 (inst*6+((step-4)*2)+clk) ->   SHL:10100111@4s  */    ALU1|TMP_s,
  /* Entry 1004 (inst*6+((step-4)*2)+clk) ->   SHL:10100111@5e  */    ALU1|R1_e|Ctmp_e,
  /* Entry 1005 (inst*6+((step-4)*2)+clk) ->   SHL:10100111@5s  */    ALU1|ACC_s|FLAGS_s,
  /* Entry 1006 (inst*6+((step-4)*2)+clk) ->   SHL:10100111@6e  */    ALU1|ACC_e,
  /* Entry 1007 (inst*6+((step-4)*2)+clk) ->   SHL:10100111@6s  */    R3_s,
  /* Entry 1008 (inst*6+((step-4)*2)+clk) ->   SHL:10101000@4e  */    ALU1|R0_e,
  /* Entry 1009 (inst*6+((step-4)*2)+clk) ->   SHL:10101000@4s  */    ALU1|TMP_s,
  /* Entry 1010 (inst*6+((step-4)*2)+clk) ->   SHL:10101000@5e  */    ALU1|R2_e|Ctmp_e,
  /* Entry 1011 (inst*6+((step-4)*2)+clk) ->   SHL:10101000@5s  */    ALU1|ACC_s|FLAGS_s,
  /* Entry 1012 (inst*6+((step-4)*2)+clk) ->   SHL:10101000@6e  */    ALU1|ACC_e,
  /* Entry 1013 (inst*6+((step-4)*2)+clk) ->   SHL:10101000@6s  */    R0_s,
  /* Entry 1014 (inst*6+((step-4)*2)+clk) ->   SHL:10101001@4e  */    ALU1|R1_e,
  /* Entry 1015 (inst*6+((step-4)*2)+clk) ->   SHL:10101001@4s  */    ALU1|TMP_s,
  /* Entry 1016 (inst*6+((step-4)*2)+clk) ->   SHL:10101001@5e  */    ALU1|R2_e|Ctmp_e,
  /* Entry 1017 (inst*6+((step-4)*2)+clk) ->   SHL:10101001@5s  */    ALU1|ACC_s|FLAGS_s,
  /* Entry 1018 (inst*6+((step-4)*2)+clk) ->   SHL:10101001@6e  */    ALU1|ACC_e,
  /* Entry 1019 (inst*6+((step-4)*2)+clk) ->   SHL:10101001@6s  */    R1_s,
  /* Entry 1020 (inst*6+((step-4)*2)+clk) ->   SHL:10101010@4e  */    ALU1|R2_e,
  /* Entry 1021 (inst*6+((step-4)*2)+clk) ->   SHL:10101010@4s  */    ALU1|TMP_s,
  /* Entry 1022 (inst*6+((step-4)*2)+clk) ->   SHL:10101010@5e  */    ALU1|R2_e|Ctmp_e,
  /* Entry 1023 (inst*6+((step-4)*2)+clk) ->   SHL:10101010@5s  */    ALU1|ACC_s|FLAGS_s,
  /* Entry 1024 (inst*6+((step-4)*2)+clk) ->   SHL:10101010@6e  */    ALU1|ACC_e,
  /* Entry 1025 (inst*6+((step-4)*2)+clk) ->   SHL:10101010@6s  */    R2_s,
  /* Entry 1026 (inst*6+((step-4)*2)+clk) ->   SHL:10101011@4e  */    ALU1|R3_e,
  /* Entry 1027 (inst*6+((step-4)*2)+clk) ->   SHL:10101011@4s  */    ALU1|TMP_s,
  /* Entry 1028 (inst*6+((step-4)*2)+clk) ->   SHL:10101011@5e  */    ALU1|R2_e|Ctmp_e,
  /* Entry 1029 (inst*6+((step-4)*2)+clk) ->   SHL:10101011@5s  */    ALU1|ACC_s|FLAGS_s,
  /* Entry 1030 (inst*6+((step-4)*2)+clk) ->   SHL:10101011@6e  */    ALU1|ACC_e,
  /* Entry 1031 (inst*6+((step-4)*2)+clk) ->   SHL:10101011@6s  */    R3_s,
  /* Entry 1032 (inst*6+((step-4)*2)+clk) ->   SHL:10101100@4e  */    ALU1|R0_e,
  /* Entry 1033 (inst*6+((step-4)*2)+clk) ->   SHL:10101100@4s  */    ALU1|TMP_s,
  /* Entry 1034 (inst*6+((step-4)*2)+clk) ->   SHL:10101100@5e  */    ALU1|R3_e|Ctmp_e,
  /* Entry 1035 (inst*6+((step-4)*2)+clk) ->   SHL:10101100@5s  */    ALU1|ACC_s|FLAGS_s,
  /* Entry 1036 (inst*6+((step-4)*2)+clk) ->   SHL:10101100@6e  */    ALU1|ACC_e,
  /* Entry 1037 (inst*6+((step-4)*2)+clk) ->   SHL:10101100@6s  */    R0_s,
  /* Entry 1038 (inst*6+((step-4)*2)+clk) ->   SHL:10101101@4e  */    ALU1|R1_e,
  /* Entry 1039 (inst*6+((step-4)*2)+clk) ->   SHL:10101101@4s  */    ALU1|TMP_s,
  /* Entry 1040 (inst*6+((step-4)*2)+clk) ->   SHL:10101101@5e  */    ALU1|R3_e|Ctmp_e,
  /* Entry 1041 (inst*6+((step-4)*2)+clk) ->   SHL:10101101@5s  */    ALU1|ACC_s|FLAGS_s,
  /* Entry 1042 (inst*6+((step-4)*2)+clk) ->   SHL:10101101@6e  */    ALU1|ACC_e,
  /* Entry 1043 (inst*6+((step-4)*2)+clk) ->   SHL:10101101@6s  */    R1_s,
  /* Entry 1044 (inst*6+((step-4)*2)+clk) ->   SHL:10101110@4e  */    ALU1|R2_e,
  /* Entry 1045 (inst*6+((step-4)*2)+clk) ->   SHL:10101110@4s  */    ALU1|TMP_s,
  /* Entry 1046 (inst*6+((step-4)*2)+clk) ->   SHL:10101110@5e  */    ALU1|R3_e|Ctmp_e,
  /* Entry 1047 (inst*6+((step-4)*2)+clk) ->   SHL:10101110@5s  */    ALU1|ACC_s|FLAGS_s,
  /* Entry 1048 (inst*6+((step-4)*2)+clk) ->   SHL:10101110@6e  */    ALU1|ACC_e,
  /* Entry 1049 (inst*6+((step-4)*2)+clk) ->   SHL:10101110@6s  */    R2_s,
  /* Entry 1050 (inst*6+((step-4)*2)+clk) ->   SHL:10101111@4e  */    ALU1|R3_e,
  /* Entry 1051 (inst*6+((step-4)*2)+clk) ->   SHL:10101111@4s  */    ALU1|TMP_s,
  /* Entry 1052 (inst*6+((step-4)*2)+clk) ->   SHL:10101111@5e  */    ALU1|R3_e|Ctmp_e,
  /* Entry 1053 (inst*6+((step-4)*2)+clk) ->   SHL:10101111@5s  */    ALU1|ACC_s|FLAGS_s,
  /* Entry 1054 (inst*6+((step-4)*2)+clk) ->   SHL:10101111@6e  */    ALU1|ACC_e,
  /* Entry 1055 (inst*6+((step-4)*2)+clk) ->   SHL:10101111@6s  */    R3_s,
  /* Entry 1056 (inst*6+((step-4)*2)+clk) ->   NOT:10110000@4e  */    ALU1|ALU0|R0_e,
  /* Entry 1057 (inst*6+((step-4)*2)+clk) ->   NOT:10110000@4s  */    ALU1|ALU0|TMP_s,
  /* Entry 1058 (inst*6+((step-4)*2)+clk) ->   NOT:10110000@5e  */    ALU1|ALU0|R0_e|Ctmp_e,
  /* Entry 1059 (inst*6+((step-4)*2)+clk) ->   NOT:10110000@5s  */    ALU1|ALU0|ACC_s|FLAGS_s,
  /* Entry 1060 (inst*6+((step-4)*2)+clk) ->   NOT:10110000@6e  */    ALU1|ALU0|ACC_e,
  /* Entry 1061 (inst*6+((step-4)*2)+clk) ->   NOT:10110000@6s  */    R0_s,
  /* Entry 1062 (inst*6+((step-4)*2)+clk) ->   NOT:10110001@4e  */    ALU1|ALU0|R1_e,
  /* Entry 1063 (inst*6+((step-4)*2)+clk) ->   NOT:10110001@4s  */    ALU1|ALU0|TMP_s,
  /* Entry 1064 (inst*6+((step-4)*2)+clk) ->   NOT:10110001@5e  */    ALU1|ALU0|R0_e|Ctmp_e,
  /* Entry 1065 (inst*6+((step-4)*2)+clk) ->   NOT:10110001@5s  */    ALU1|ALU0|ACC_s|FLAGS_s,
  /* Entry 1066 (inst*6+((step-4)*2)+clk) ->   NOT:10110001@6e  */    ALU1|ALU0|ACC_e,
  /* Entry 1067 (inst*6+((step-4)*2)+clk) ->   NOT:10110001@6s  */    R1_s,
  /* Entry 1068 (inst*6+((step-4)*2)+clk) ->   NOT:10110010@4e  */    ALU1|ALU0|R2_e,
  /* Entry 1069 (inst*6+((step-4)*2)+clk) ->   NOT:10110010@4s  */    ALU1|ALU0|TMP_s,
  /* Entry 1070 (inst*6+((step-4)*2)+clk) ->   NOT:10110010@5e  */    ALU1|ALU0|R0_e|Ctmp_e,
  /* Entry 1071 (inst*6+((step-4)*2)+clk) ->   NOT:10110010@5s  */    ALU1|ALU0|ACC_s|FLAGS_s,
  /* Entry 1072 (inst*6+((step-4)*2)+clk) ->   NOT:10110010@6e  */    ALU1|ALU0|ACC_e,
  /* Entry 1073 (inst*6+((step-4)*2)+clk) ->   NOT:10110010@6s  */    R2_s,
  /* Entry 1074 (inst*6+((step-4)*2)+clk) ->   NOT:10110011@4e  */    ALU1|ALU0|R3_e,
  /* Entry 1075 (inst*6+((step-4)*2)+clk) ->   NOT:10110011@4s  */    ALU1|ALU0|TMP_s,
  /* Entry 1076 (inst*6+((step-4)*2)+clk) ->   NOT:10110011@5e  */    ALU1|ALU0|R0_e|Ctmp_e,
  /* Entry 1077 (inst*6+((step-4)*2)+clk) ->   NOT:10110011@5s  */    ALU1|ALU0|ACC_s|FLAGS_s,
  /* Entry 1078 (inst*6+((step-4)*2)+clk) ->   NOT:10110011@6e  */    ALU1|ALU0|ACC_e,
  /* Entry 1079 (inst*6+((step-4)*2)+clk) ->   NOT:10110011@6s  */    R3_s,
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
  /* Entry 1128 (inst*6+((step-4)*2)+clk) ->   NOT:10111100@4e  */    ALU1|ALU0|R0_e,
  /* Entry 1129 (inst*6+((step-4)*2)+clk) ->   NOT:10111100@4s  */    ALU1|ALU0|TMP_s,
  /* Entry 1130 (inst*6+((step-4)*2)+clk) ->   NOT:10111100@5e  */    ALU1|ALU0|R3_e|Ctmp_e,
  /* Entry 1131 (inst*6+((step-4)*2)+clk) ->   NOT:10111100@5s  */    ALU1|ALU0|ACC_s|FLAGS_s,
  /* Entry 1132 (inst*6+((step-4)*2)+clk) ->   NOT:10111100@6e  */    ALU1|ALU0|ACC_e,
  /* Entry 1133 (inst*6+((step-4)*2)+clk) ->   NOT:10111100@6s  */    R0_s,
  /* Entry 1134 (inst*6+((step-4)*2)+clk) ->   NOT:10111101@4e  */    ALU1|ALU0|R1_e,
  /* Entry 1135 (inst*6+((step-4)*2)+clk) ->   NOT:10111101@4s  */    ALU1|ALU0|TMP_s,
  /* Entry 1136 (inst*6+((step-4)*2)+clk) ->   NOT:10111101@5e  */    ALU1|ALU0|R3_e|Ctmp_e,
  /* Entry 1137 (inst*6+((step-4)*2)+clk) ->   NOT:10111101@5s  */    ALU1|ALU0|ACC_s|FLAGS_s,
  /* Entry 1138 (inst*6+((step-4)*2)+clk) ->   NOT:10111101@6e  */    ALU1|ALU0|ACC_e,
  /* Entry 1139 (inst*6+((step-4)*2)+clk) ->   NOT:10111101@6s  */    R1_s,
  /* Entry 1140 (inst*6+((step-4)*2)+clk) ->   NOT:10111110@4e  */    ALU1|ALU0|R2_e,
  /* Entry 1141 (inst*6+((step-4)*2)+clk) ->   NOT:10111110@4s  */    ALU1|ALU0|TMP_s,
  /* Entry 1142 (inst*6+((step-4)*2)+clk) ->   NOT:10111110@5e  */    ALU1|ALU0|R3_e|Ctmp_e,
  /* Entry 1143 (inst*6+((step-4)*2)+clk) ->   NOT:10111110@5s  */    ALU1|ALU0|ACC_s|FLAGS_s,
  /* Entry 1144 (inst*6+((step-4)*2)+clk) ->   NOT:10111110@6e  */    ALU1|ALU0|ACC_e,
  /* Entry 1145 (inst*6+((step-4)*2)+clk) ->   NOT:10111110@6s  */    R2_s,
  /* Entry 1146 (inst*6+((step-4)*2)+clk) ->   NOT:10111111@4e  */    ALU1|ALU0|R3_e,
  /* Entry 1147 (inst*6+((step-4)*2)+clk) ->   NOT:10111111@4s  */    ALU1|ALU0|TMP_s,
  /* Entry 1148 (inst*6+((step-4)*2)+clk) ->   NOT:10111111@5e  */    ALU1|ALU0|R3_e|Ctmp_e,
  /* Entry 1149 (inst*6+((step-4)*2)+clk) ->   NOT:10111111@5s  */    ALU1|ALU0|ACC_s|FLAGS_s,
  /* Entry 1150 (inst*6+((step-4)*2)+clk) ->   NOT:10111111@6e  */    ALU1|ALU0|ACC_e,
  /* Entry 1151 (inst*6+((step-4)*2)+clk) ->   NOT:10111111@6s  */    R3_s,
  /* Entry 1152 (inst*6+((step-4)*2)+clk) ->   AND:11000000@4e  */    ALU2|R0_e,
  /* Entry 1153 (inst*6+((step-4)*2)+clk) ->   AND:11000000@4s  */    ALU2|TMP_s,
  /* Entry 1154 (inst*6+((step-4)*2)+clk) ->   AND:11000000@5e  */    ALU2|R0_e|Ctmp_e,
  /* Entry 1155 (inst*6+((step-4)*2)+clk) ->   AND:11000000@5s  */    ALU2|ACC_s|FLAGS_s,
  /* Entry 1156 (inst*6+((step-4)*2)+clk) ->   AND:11000000@6e  */    ALU2|ACC_e,
  /* Entry 1157 (inst*6+((step-4)*2)+clk) ->   AND:11000000@6s  */    R0_s,
  /* Entry 1158 (inst*6+((step-4)*2)+clk) ->   AND:11000001@4e  */    ALU2|R1_e,
  /* Entry 1159 (inst*6+((step-4)*2)+clk) ->   AND:11000001@4s  */    ALU2|TMP_s,
  /* Entry 1160 (inst*6+((step-4)*2)+clk) ->   AND:11000001@5e  */    ALU2|R0_e|Ctmp_e,
  /* Entry 1161 (inst*6+((step-4)*2)+clk) ->   AND:11000001@5s  */    ALU2|ACC_s|FLAGS_s,
  /* Entry 1162 (inst*6+((step-4)*2)+clk) ->   AND:11000001@6e  */    ALU2|ACC_e,
  /* Entry 1163 (inst*6+((step-4)*2)+clk) ->   AND:11000001@6s  */    R1_s,
  /* Entry 1164 (inst*6+((step-4)*2)+clk) ->   AND:11000010@4e  */    ALU2|R2_e,
  /* Entry 1165 (inst*6+((step-4)*2)+clk) ->   AND:11000010@4s  */    ALU2|TMP_s,
  /* Entry 1166 (inst*6+((step-4)*2)+clk) ->   AND:11000010@5e  */    ALU2|R0_e|Ctmp_e,
  /* Entry 1167 (inst*6+((step-4)*2)+clk) ->   AND:11000010@5s  */    ALU2|ACC_s|FLAGS_s,
  /* Entry 1168 (inst*6+((step-4)*2)+clk) ->   AND:11000010@6e  */    ALU2|ACC_e,
  /* Entry 1169 (inst*6+((step-4)*2)+clk) ->   AND:11000010@6s  */    R2_s,
  /* Entry 1170 (inst*6+((step-4)*2)+clk) ->   AND:11000011@4e  */    ALU2|R3_e,
  /* Entry 1171 (inst*6+((step-4)*2)+clk) ->   AND:11000011@4s  */    ALU2|TMP_s,
  /* Entry 1172 (inst*6+((step-4)*2)+clk) ->   AND:11000011@5e  */    ALU2|R0_e|Ctmp_e,
  /* Entry 1173 (inst*6+((step-4)*2)+clk) ->   AND:11000011@5s  */    ALU2|ACC_s|FLAGS_s,
  /* Entry 1174 (inst*6+((step-4)*2)+clk) ->   AND:11000011@6e  */    ALU2|ACC_e,
  /* Entry 1175 (inst*6+((step-4)*2)+clk) ->   AND:11000011@6s  */    R3_s,
  /* Entry 1176 (inst*6+((step-4)*2)+clk) ->   AND:11000100@4e  */    ALU2|R0_e,
  /* Entry 1177 (inst*6+((step-4)*2)+clk) ->   AND:11000100@4s  */    ALU2|TMP_s,
  /* Entry 1178 (inst*6+((step-4)*2)+clk) ->   AND:11000100@5e  */    ALU2|R1_e|Ctmp_e,
  /* Entry 1179 (inst*6+((step-4)*2)+clk) ->   AND:11000100@5s  */    ALU2|ACC_s|FLAGS_s,
  /* Entry 1180 (inst*6+((step-4)*2)+clk) ->   AND:11000100@6e  */    ALU2|ACC_e,
  /* Entry 1181 (inst*6+((step-4)*2)+clk) ->   AND:11000100@6s  */    R0_s,
  /* Entry 1182 (inst*6+((step-4)*2)+clk) ->   AND:11000101@4e  */    ALU2|R1_e,
  /* Entry 1183 (inst*6+((step-4)*2)+clk) ->   AND:11000101@4s  */    ALU2|TMP_s,
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
  /* Entry 1235 (inst*6+((step-4)*2)+clk) ->   AND:11001101@6s  */    R1_s,
  /* Entry 1236 (inst*6+((step-4)*2)+clk) ->   AND:11001110@4e  */    ALU2|R2_e,
  /* Entry 1237 (inst*6+((step-4)*2)+clk) ->   AND:11001110@4s  */    ALU2|TMP_s,
  /* Entry 1238 (inst*6+((step-4)*2)+clk) ->   AND:11001110@5e  */    ALU2|R3_e|Ctmp_e,
  /* Entry 1239 (inst*6+((step-4)*2)+clk) ->   AND:11001110@5s  */    ALU2|ACC_s|FLAGS_s,
  /* Entry 1240 (inst*6+((step-4)*2)+clk) ->   AND:11001110@6e  */    ALU2|ACC_e,
  /* Entry 1241 (inst*6+((step-4)*2)+clk) ->   AND:11001110@6s  */    R2_s,
  /* Entry 1242 (inst*6+((step-4)*2)+clk) ->   AND:11001111@4e  */    ALU2|R3_e,
  /* Entry 1243 (inst*6+((step-4)*2)+clk) ->   AND:11001111@4s  */    ALU2|TMP_s,
  /* Entry 1244 (inst*6+((step-4)*2)+clk) ->   AND:11001111@5e  */    ALU2|R3_e|Ctmp_e,
  /* Entry 1245 (inst*6+((step-4)*2)+clk) ->   AND:11001111@5s  */    ALU2|ACC_s|FLAGS_s,
  /* Entry 1246 (inst*6+((step-4)*2)+clk) ->   AND:11001111@6e  */    ALU2|ACC_e,
  /* Entry 1247 (inst*6+((step-4)*2)+clk) ->   AND:11001111@6s  */    R3_s,
  /* Entry 1248 (inst*6+((step-4)*2)+clk) ->    OR:11010000@4e  */    ALU2|ALU0|R0_e,
  /* Entry 1249 (inst*6+((step-4)*2)+clk) ->    OR:11010000@4s  */    ALU2|ALU0|TMP_s,
  /* Entry 1250 (inst*6+((step-4)*2)+clk) ->    OR:11010000@5e  */    ALU2|ALU0|R0_e|Ctmp_e,
  /* Entry 1251 (inst*6+((step-4)*2)+clk) ->    OR:11010000@5s  */    ALU2|ALU0|ACC_s|FLAGS_s,
  /* Entry 1252 (inst*6+((step-4)*2)+clk) ->    OR:11010000@6e  */    ALU2|ALU0|ACC_e,
  /* Entry 1253 (inst*6+((step-4)*2)+clk) ->    OR:11010000@6s  */    R0_s,
  /* Entry 1254 (inst*6+((step-4)*2)+clk) ->    OR:11010001@4e  */    ALU2|ALU0|R1_e,
  /* Entry 1255 (inst*6+((step-4)*2)+clk) ->    OR:11010001@4s  */    ALU2|ALU0|TMP_s,
  /* Entry 1256 (inst*6+((step-4)*2)+clk) ->    OR:11010001@5e  */    ALU2|ALU0|R0_e|Ctmp_e,
  /* Entry 1257 (inst*6+((step-4)*2)+clk) ->    OR:11010001@5s  */    ALU2|ALU0|ACC_s|FLAGS_s,
  /* Entry 1258 (inst*6+((step-4)*2)+clk) ->    OR:11010001@6e  */    ALU2|ALU0|ACC_e,
  /* Entry 1259 (inst*6+((step-4)*2)+clk) ->    OR:11010001@6s  */    R1_s,
  /* Entry 1260 (inst*6+((step-4)*2)+clk) ->    OR:11010010@4e  */    ALU2|ALU0|R2_e,
  /* Entry 1261 (inst*6+((step-4)*2)+clk) ->    OR:11010010@4s  */    ALU2|ALU0|TMP_s,
  /* Entry 1262 (inst*6+((step-4)*2)+clk) ->    OR:11010010@5e  */    ALU2|ALU0|R0_e|Ctmp_e,
  /* Entry 1263 (inst*6+((step-4)*2)+clk) ->    OR:11010010@5s  */    ALU2|ALU0|ACC_s|FLAGS_s,
  /* Entry 1264 (inst*6+((step-4)*2)+clk) ->    OR:11010010@6e  */    ALU2|ALU0|ACC_e,
  /* Entry 1265 (inst*6+((step-4)*2)+clk) ->    OR:11010010@6s  */    R2_s,
  /* Entry 1266 (inst*6+((step-4)*2)+clk) ->    OR:11010011@4e  */    ALU2|ALU0|R3_e,
  /* Entry 1267 (inst*6+((step-4)*2)+clk) ->    OR:11010011@4s  */    ALU2|ALU0|TMP_s,
  /* Entry 1268 (inst*6+((step-4)*2)+clk) ->    OR:11010011@5e  */    ALU2|ALU0|R0_e|Ctmp_e,
  /* Entry 1269 (inst*6+((step-4)*2)+clk) ->    OR:11010011@5s  */    ALU2|ALU0|ACC_s|FLAGS_s,
  /* Entry 1270 (inst*6+((step-4)*2)+clk) ->    OR:11010011@6e  */    ALU2|ALU0|ACC_e,
  /* Entry 1271 (inst*6+((step-4)*2)+clk) ->    OR:11010011@6s  */    R3_s,
  /* Entry 1272 (inst*6+((step-4)*2)+clk) ->    OR:11010100@4e  */    ALU2|ALU0|R0_e,
  /* Entry 1273 (inst*6+((step-4)*2)+clk) ->    OR:11010100@4s  */    ALU2|ALU0|TMP_s,
  /* Entry 1274 (inst*6+((step-4)*2)+clk) ->    OR:11010100@5e  */    ALU2|ALU0|R1_e|Ctmp_e,
  /* Entry 1275 (inst*6+((step-4)*2)+clk) ->    OR:11010100@5s  */    ALU2|ALU0|ACC_s|FLAGS_s,
  /* Entry 1276 (inst*6+((step-4)*2)+clk) ->    OR:11010100@6e  */    ALU2|ALU0|ACC_e,
  /* Entry 1277 (inst*6+((step-4)*2)+clk) ->    OR:11010100@6s  */    R0_s,
  /* Entry 1278 (inst*6+((step-4)*2)+clk) ->    OR:11010101@4e  */    ALU2|ALU0|R1_e,
  /* Entry 1279 (inst*6+((step-4)*2)+clk) ->    OR:11010101@4s  */    ALU2|ALU0|TMP_s,
  /* Entry 1280 (inst*6+((step-4)*2)+clk) ->    OR:11010101@5e  */    ALU2|ALU0|R1_e|Ctmp_e,
  /* Entry 1281 (inst*6+((step-4)*2)+clk) ->    OR:11010101@5s  */    ALU2|ALU0|ACC_s|FLAGS_s,
  /* Entry 1282 (inst*6+((step-4)*2)+clk) ->    OR:11010101@6e  */    ALU2|ALU0|ACC_e,
  /* Entry 1283 (inst*6+((step-4)*2)+clk) ->    OR:11010101@6s  */    R1_s,
  /* Entry 1284 (inst*6+((step-4)*2)+clk) ->    OR:11010110@4e  */    ALU2|ALU0|R2_e,
  /* Entry 1285 (inst*6+((step-4)*2)+clk) ->    OR:11010110@4s  */    ALU2|ALU0|TMP_s,
  /* Entry 1286 (inst*6+((step-4)*2)+clk) ->    OR:11010110@5e  */    ALU2|ALU0|R1_e|Ctmp_e,
  /* Entry 1287 (inst*6+((step-4)*2)+clk) ->    OR:11010110@5s  */    ALU2|ALU0|ACC_s|FLAGS_s,
  /* Entry 1288 (inst*6+((step-4)*2)+clk) ->    OR:11010110@6e  */    ALU2|ALU0|ACC_e,
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
  /* Entry 1371 (inst*6+((step-4)*2)+clk) ->   XOR:11100100@5s  */    ALU2|ALU1|ACC_s|FLAGS_s,
  /* Entry 1372 (inst*6+((step-4)*2)+clk) ->   XOR:11100100@6e  */    ALU2|ALU1|ACC_e,
  /* Entry 1373 (inst*6+((step-4)*2)+clk) ->   XOR:11100100@6s  */    R0_s,
  /* Entry 1374 (inst*6+((step-4)*2)+clk) ->   XOR:11100101@4e  */    ALU2|ALU1|R1_e,
  /* Entry 1375 (inst*6+((step-4)*2)+clk) ->   XOR:11100101@4s  */    ALU2|ALU1|TMP_s,
  /* Entry 1376 (inst*6+((step-4)*2)+clk) ->   XOR:11100101@5e  */    ALU2|ALU1|R1_e|Ctmp_e,
  /* Entry 1377 (inst*6+((step-4)*2)+clk) ->   XOR:11100101@5s  */    ALU2|ALU1|ACC_s|FLAGS_s,
  /* Entry 1378 (inst*6+((step-4)*2)+clk) ->   XOR:11100101@6e  */    ALU2|ALU1|ACC_e,
  /* Entry 1379 (inst*6+((step-4)*2)+clk) ->   XOR:11100101@6s  */    R1_s,
  /* Entry 1380 (inst*6+((step-4)*2)+clk) ->   XOR:11100110@4e  */    ALU2|ALU1|R2_e,
  /* Entry 1381 (inst*6+((step-4)*2)+clk) ->   XOR:11100110@4s  */    ALU2|ALU1|TMP_s,
  /* Entry 1382 (inst*6+((step-4)*2)+clk) ->   XOR:11100110@5e  */    ALU2|ALU1|R1_e|Ctmp_e,
  /* Entry 1383 (inst*6+((step-4)*2)+clk) ->   XOR:11100110@5s  */    ALU2|ALU1|ACC_s|FLAGS_s,
  /* Entry 1384 (inst*6+((step-4)*2)+clk) ->   XOR:11100110@6e  */    ALU2|ALU1|ACC_e,
  /* Entry 1385 (inst*6+((step-4)*2)+clk) ->   XOR:11100110@6s  */    R2_s,
  /* Entry 1386 (inst*6+((step-4)*2)+clk) ->   XOR:11100111@4e  */    ALU2|ALU1|R3_e,
  /* Entry 1387 (inst*6+((step-4)*2)+clk) ->   XOR:11100111@4s  */    ALU2|ALU1|TMP_s,
  /* Entry 1388 (inst*6+((step-4)*2)+clk) ->   XOR:11100111@5e  */    ALU2|ALU1|R1_e|Ctmp_e,
  /* Entry 1389 (inst*6+((step-4)*2)+clk) ->   XOR:11100111@5s  */    ALU2|ALU1|ACC_s|FLAGS_s,
  /* Entry 1390 (inst*6+((step-4)*2)+clk) ->   XOR:11100111@6e  */    ALU2|ALU1|ACC_e,
  /* Entry 1391 (inst*6+((step-4)*2)+clk) ->   XOR:11100111@6s  */    R3_s,
  /* Entry 1392 (inst*6+((step-4)*2)+clk) ->   XOR:11101000@4e  */    ALU2|ALU1|R0_e,
  /* Entry 1393 (inst*6+((step-4)*2)+clk) ->   XOR:11101000@4s  */    ALU2|ALU1|TMP_s,
  /* Entry 1394 (inst*6+((step-4)*2)+clk) ->   XOR:11101000@5e  */    ALU2|ALU1|R2_e|Ctmp_e,
  /* Entry 1395 (inst*6+((step-4)*2)+clk) ->   XOR:11101000@5s  */    ALU2|ALU1|ACC_s|FLAGS_s,
  /* Entry 1396 (inst*6+((step-4)*2)+clk) ->   XOR:11101000@6e  */    ALU2|ALU1|ACC_e,
  /* Entry 1397 (inst*6+((step-4)*2)+clk) ->   XOR:11101000@6s  */    R0_s,
  /* Entry 1398 (inst*6+((step-4)*2)+clk) ->   XOR:11101001@4e  */    ALU2|ALU1|R1_e,
  /* Entry 1399 (inst*6+((step-4)*2)+clk) ->   XOR:11101001@4s  */    ALU2|ALU1|TMP_s,
  /* Entry 1400 (inst*6+((step-4)*2)+clk) ->   XOR:11101001@5e  */    ALU2|ALU1|R2_e|Ctmp_e,
  /* Entry 1401 (inst*6+((step-4)*2)+clk) ->   XOR:11101001@5s  */    ALU2|ALU1|ACC_s|FLAGS_s,
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
