patrickleboutillier/jcscpu-hmc/Arduino-Main/CW.cpp

#include "Arduino.h"
#include "INST.h"
#include "CW.h"


CW::CW(int pin_DATA, int pin_LATCH, int pin_CLK){
  _pin_DATA = pin_DATA ;
  _pin_LATCH = pin_LATCH ;
  _pin_CLK = pin_CLK ;
  _cache = -1 ;
  // Turn off the LEDs for the control word as early as possible...
  setup() ;
}


void CW::setup(){
  pinMode(_pin_DATA, OUTPUT) ;
  pinMode(_pin_LATCH, OUTPUT) ;
  pinMode(_pin_CLK, OUTPUT) ;

  loop(true, 0, false) ;
}


void CW::loop(bool reset, unsigned long cw, bool debug = 0){
  if (reset){
    cw = 0 ;
  }
  
  digitalWrite(_pin_LATCH, LOW) ;

  if ((debug)&&(cw != _cache)){
    Serial.print("  CW(cw:") ;
    Serial.print(print_cw(cw)) ;
    Serial.println(")") ;
  }

  shiftOut(_pin_DATA, _pin_CLK, LSBFIRST, (byte)(cw & 0xFF)) ;
  shiftOut(_pin_DATA, _pin_CLK, LSBFIRST, (byte)((cw >> 8) & 0xFF)) ;
  shiftOut(_pin_DATA, _pin_CLK, LSBFIRST, (byte)((cw >> 16) & 0xFF)) ;
  shiftOut(_pin_DATA, _pin_CLK, LSBFIRST, (byte)((cw >> 24) & 0xFF)) ;
  
  digitalWrite(_pin_LATCH, HIGH) ;
  _cache = cw ; 
}
