patrickleboutillier/jcscpu-hmc/Arduino-Main/RAM.cpp

#include "Arduino.h"
#include "RAM.h"


RAM::RAM(BUS *bus, const void *program, int pin_MAR_s, int pin_RAM_e, int pin_RAM_s){
  _bus = bus ;
  _MAR = 0 ;
  for (int i = 0 ; i < 255 ; i++){
    _RAM[i] = 0 ;
  }
  if (program != NULL){
    // Here we copy more than the length of the program, but it doesn't matter.
    memcpy_P(_RAM, program, 256) ;
  }
  
  _pin_MAR_s = pin_MAR_s ;
  _pin_RAM_e = pin_RAM_e ;
  _pin_RAM_s = pin_RAM_s ;
}


void RAM::setup(){
  pinMode(_pin_MAR_s, INPUT) ;
  pinMode(_pin_RAM_e, INPUT) ;
  pinMode(_pin_RAM_s, INPUT) ;
}


bool RAM::loop(bool debug = 0){
  if (digitalRead(_pin_MAR_s)){
    _MAR = _bus->read() ;
    if (debug){
      Serial.print("  RAM(op:mar_s, mar:") ;
      Serial.print(_MAR) ;
      Serial.println(")") ;
    }
  }
   
  if (digitalRead(_pin_RAM_s)){
    _RAM[_MAR] = _bus->read() ;
    if (debug){
      Serial.print("  RAM(op:ram_s, mar:") ;
      Serial.print(_MAR) ;
      Serial.print(", v:") ;
      Serial.print(_RAM[_MAR]) ;    
      Serial.println(")") ;
    }
  }

  bool be = false ;
  if (digitalRead(_pin_RAM_e)){
    _bus->write(_RAM[_MAR]) ;
    be = true ;
    if (debug){
      Serial.print("  RAM(op:ram_e, mar:") ;
      Serial.print(_MAR) ;
      Serial.print(", v:") ;
      Serial.print(_RAM[_MAR]) ;
      Serial.println(")") ;
    }
  }

  return be ;
}
