patrickleboutillier/jcscpu-hmc/Arduino-Main/ALU.h

#ifndef ALU_h
#define ALU_h

#include "Arduino.h"
#include "Extension.h"
#include "BUS.h"

class ALU {
  public:
    ALU(Extension *e, BUS *bus, int pin_op2, int pin_op1, int pin_op0, int pin_ci, int pin_c, int pin_a, int pin_e, int pin_z,
      int pin_TMP_s, int pin_ACC_e, int pin_ACC_s, int pin_BUS1) ;
    void setup() ;
    bool loop(bool debug = 0) ;
  private:
    int soft_alu(byte op, byte a, byte b, bool ci, bool debug) ;
    
    Extension *_e ;
    BUS *_bus ;
    byte _TMP ;
    byte _ACC ;
    byte _result ;
    int _pin_op2 ;
    int _pin_op1 ; 
    int _pin_op0 ; 
    int _pin_ci ; 
    int _pin_c ; 
    int _pin_a ; 
    int _pin_e ; 
    int _pin_z ;
    int _pin_TMP_s ;
    int _pin_ACC_e ;
    int _pin_ACC_s ;
    int _pin_BUS1 ;
} ;

#endif
